DanBar1971/open-lab-monitor/pcb/eagle/ambient-humidity-temp-therimstor-REVBsch.png

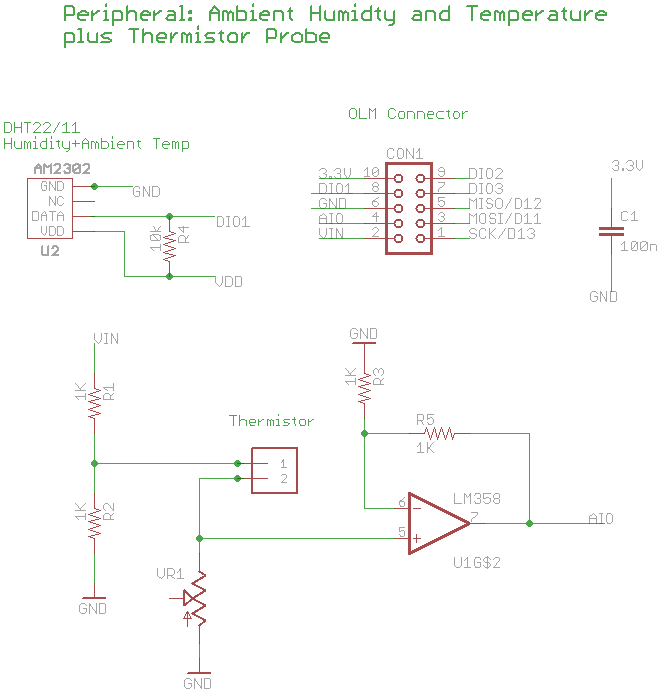
pcb/eagle/ambient-humidity-temp-therimstor-REVBsch.png
