DanBar1971/open-lab-monitor/pcb/eagle/OLM-base-v.REV-3-SMT-Board.png

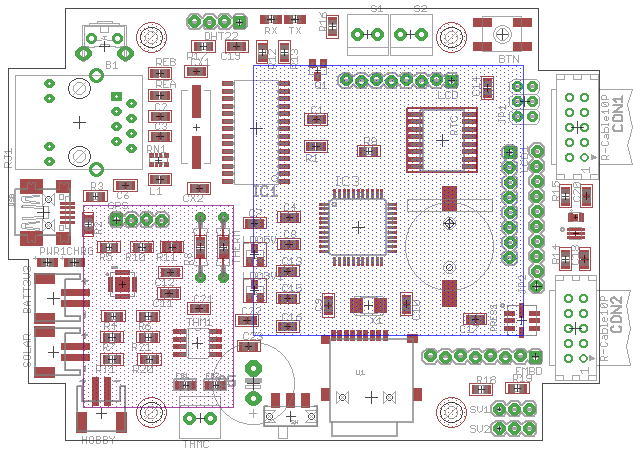
pcb/eagle/OLM-base-v.REV-3-SMT-Board.png
