DanBar1971/open-lab-monitor/pcb/eagle/OLM-base-v.REVH-SMT.png

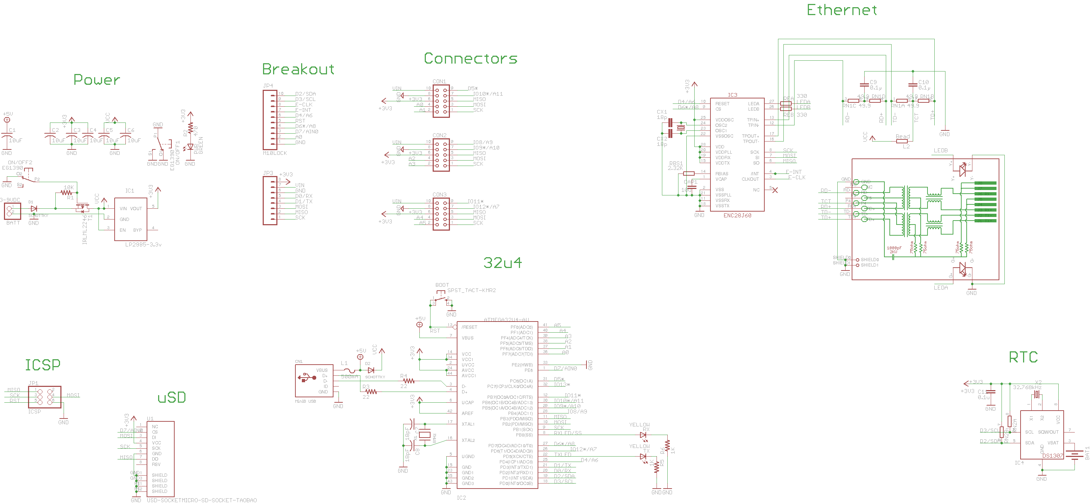
pcb/eagle/OLM-base-v.REVH-SMT.png
