DanBar1971/open-lab-monitor/pcb/eagle/OLM-base_v.REVG.png

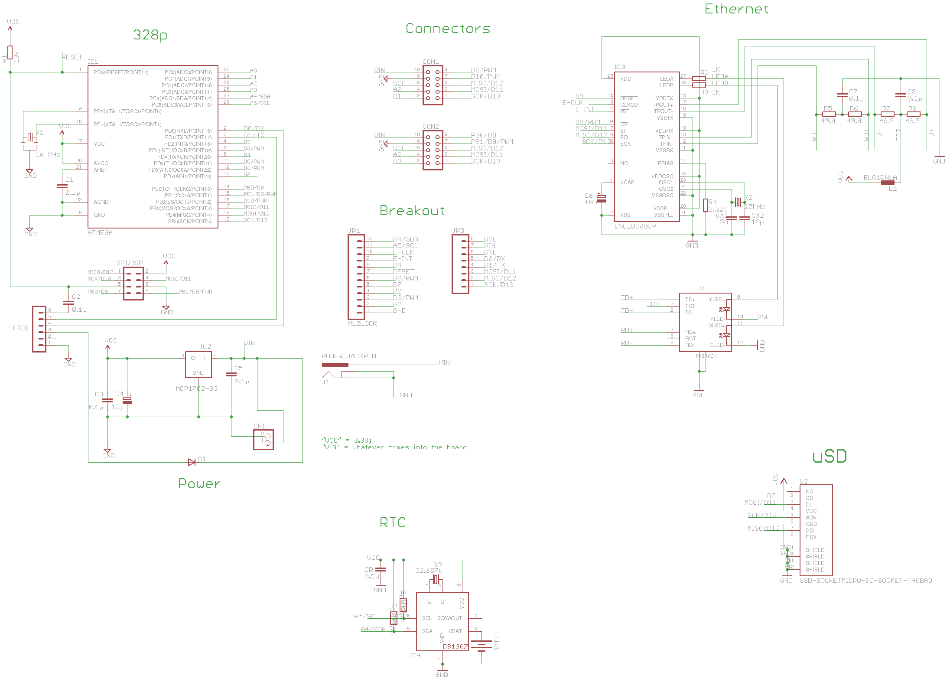
pcb/eagle/OLM-base_v.REVG.png
