DanBar1971/open-lab-monitor/pcb/eagle/olm-periph-probe+ambient+boostREVB.png

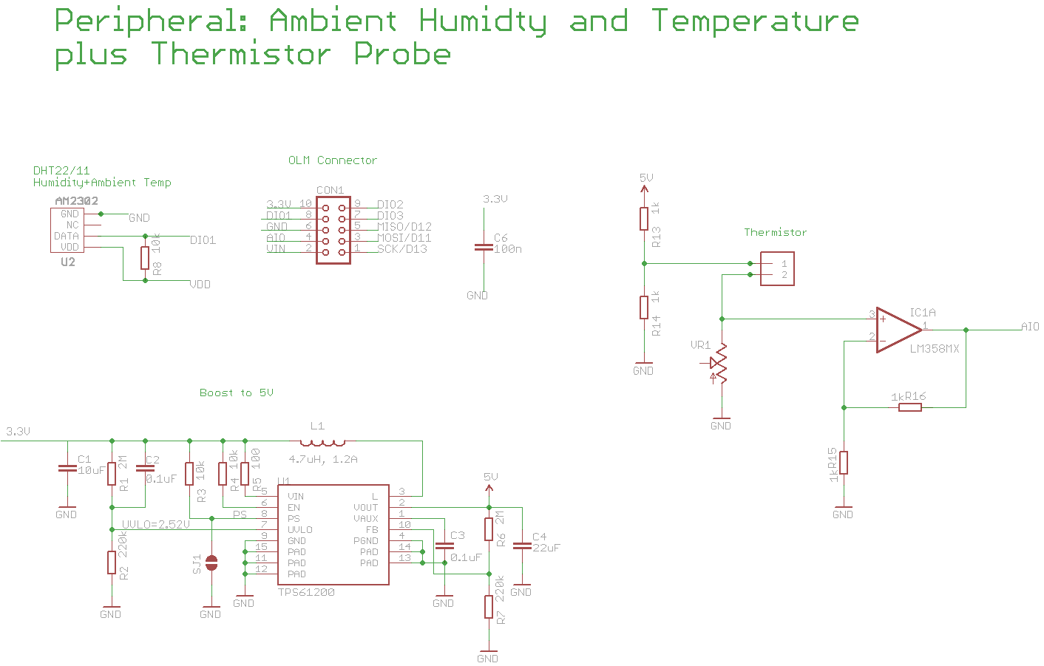
pcb/eagle/olm-periph-probe+ambient+boostREVB.png
