DanBar1971/open-lab-monitor/pcb/eagle/OLM-REV-5-brd.png

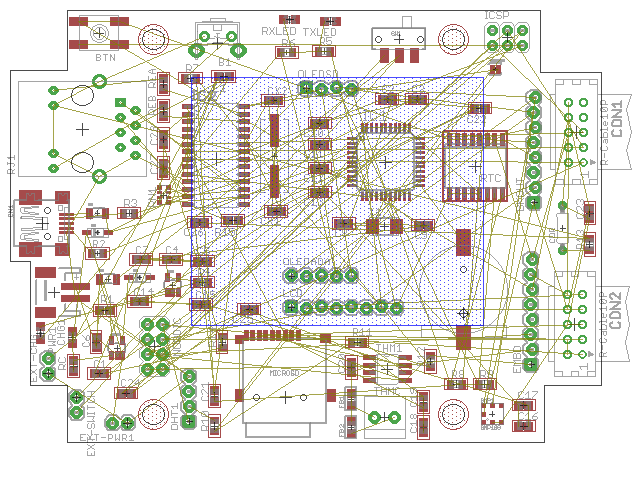
pcb/eagle/OLM-REV-5-brd.png
