DanBar1971/open-lab-monitor/pcb/eagle/OLM-REV-5-sch.png

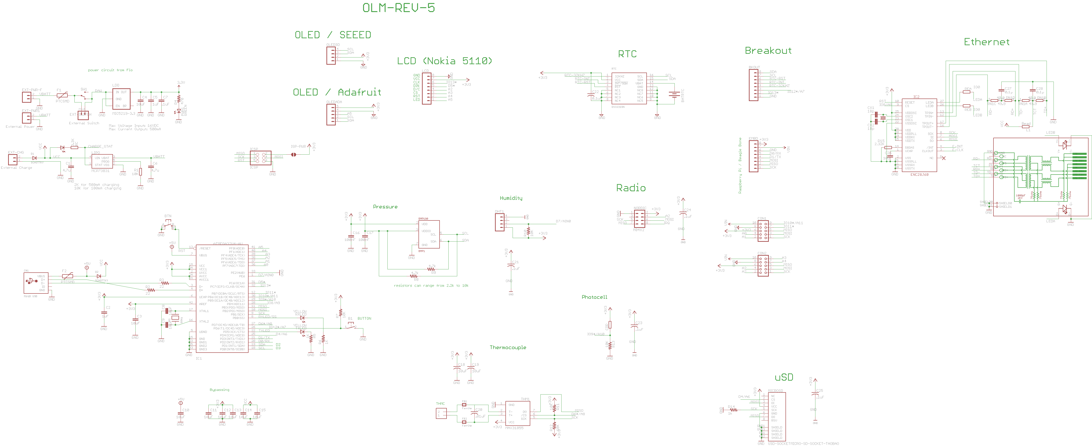
pcb/eagle/OLM-REV-5-sch.png
