DanBar1971/open-lab-monitor/pcb/eagle/OLMv11brd.png

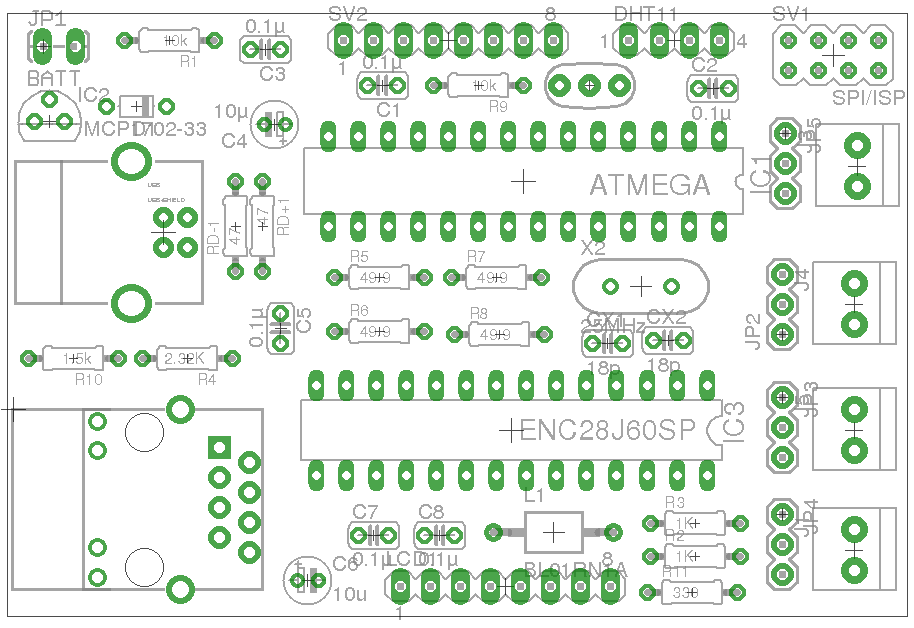
pcb/eagle/OLMv11brd.png
