DanBar1971/open-lab-monitor/pcb/eagle/OLMv11sch.png

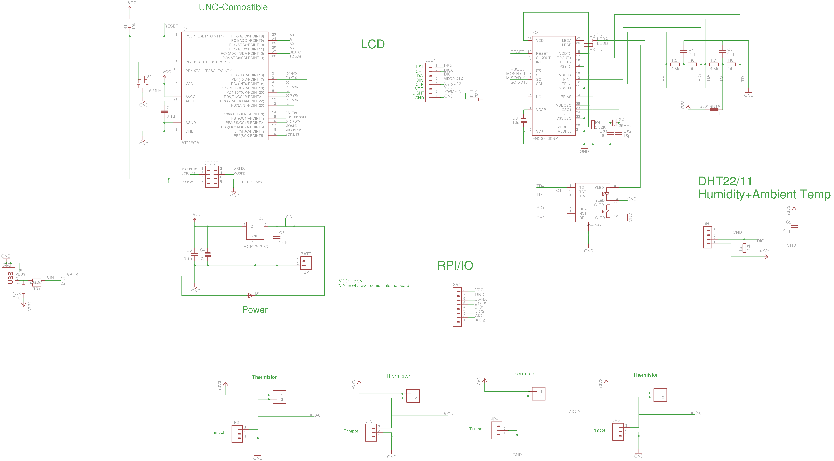
pcb/eagle/OLMv11sch.png
