DanBar1971/open-lab-monitor/pcb/eagle/OpenLux-v2-brd.png

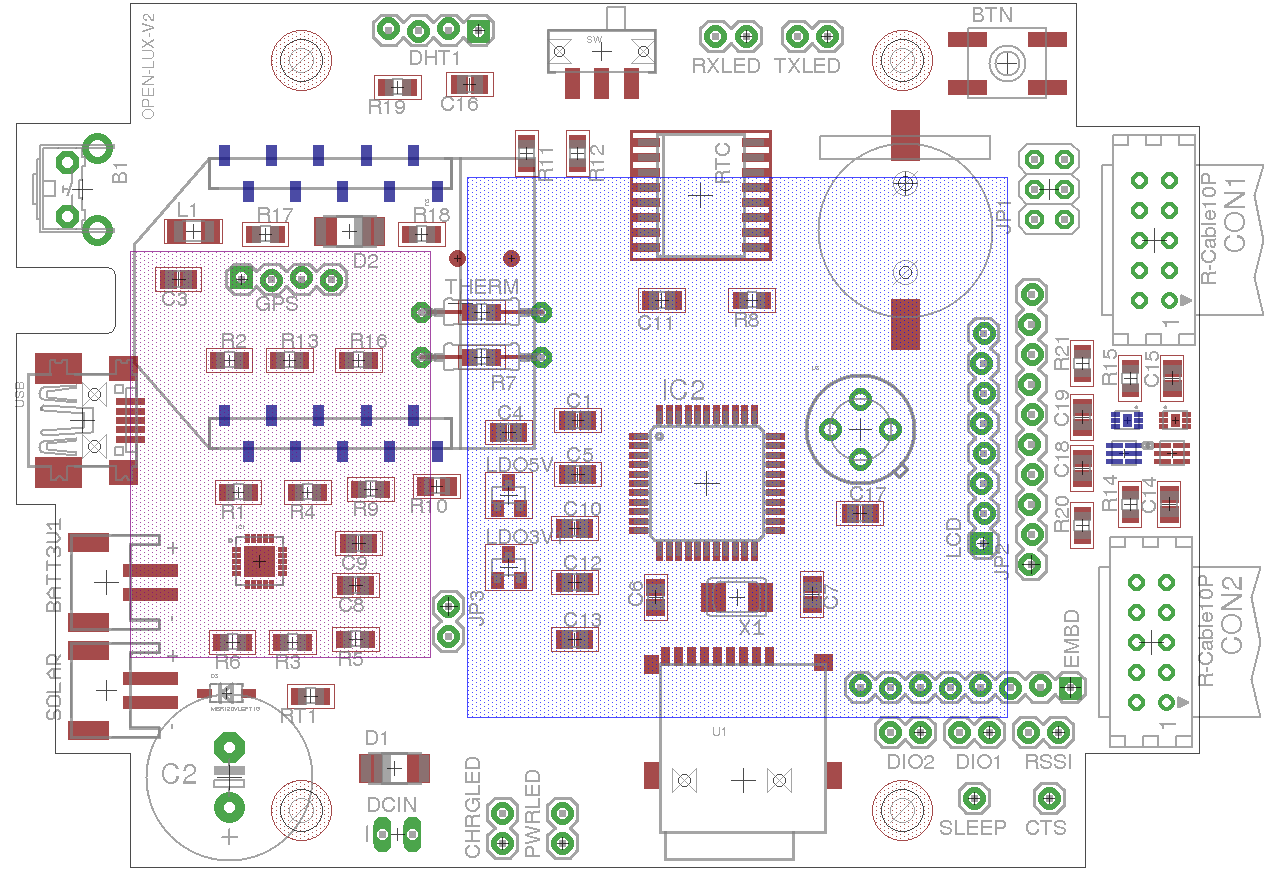
pcb/eagle/OpenLux-v2-brd.png
