DanBar1971/open-lab-monitor/pcb/eagle/OpenLux-v2-sch.png

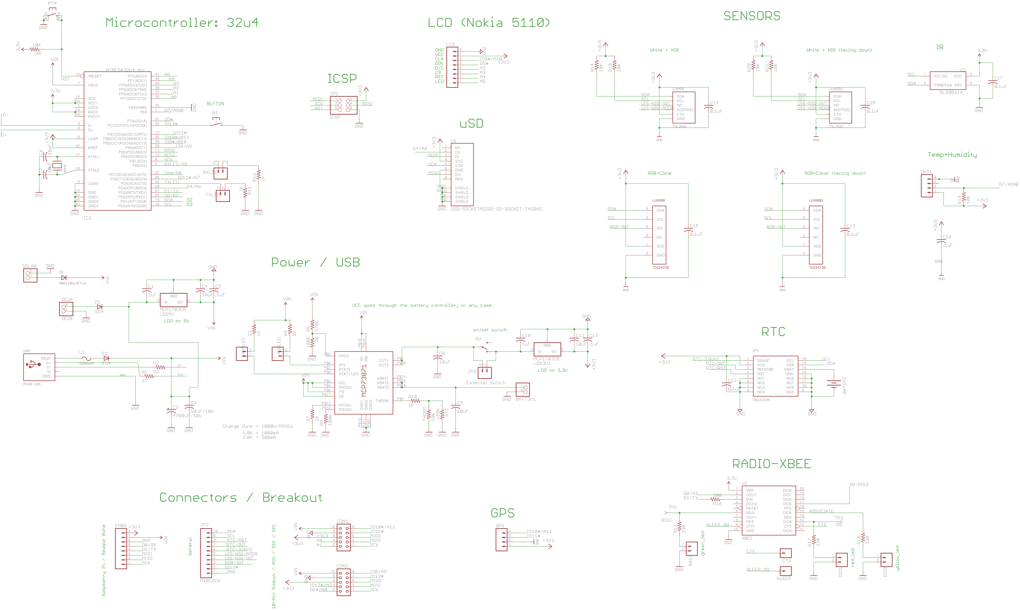
pcb/eagle/OpenLux-v2-sch.png
