DanBar1971/open-lab-monitor/pcb/eagle/VUSB/open-lab-VUSB-A-board.png

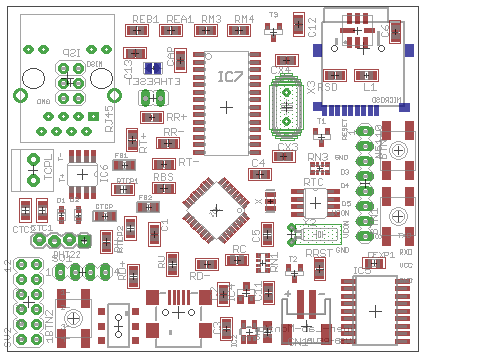
pcb/eagle/VUSB/open-lab-VUSB-A-board.png
