DanBar1971/open-lab-monitor/pcb/eagle/OpenLux-v1a.brd

## EAGLE design pcb/eagle/OpenLux-v1a.brd (2013-09-16)

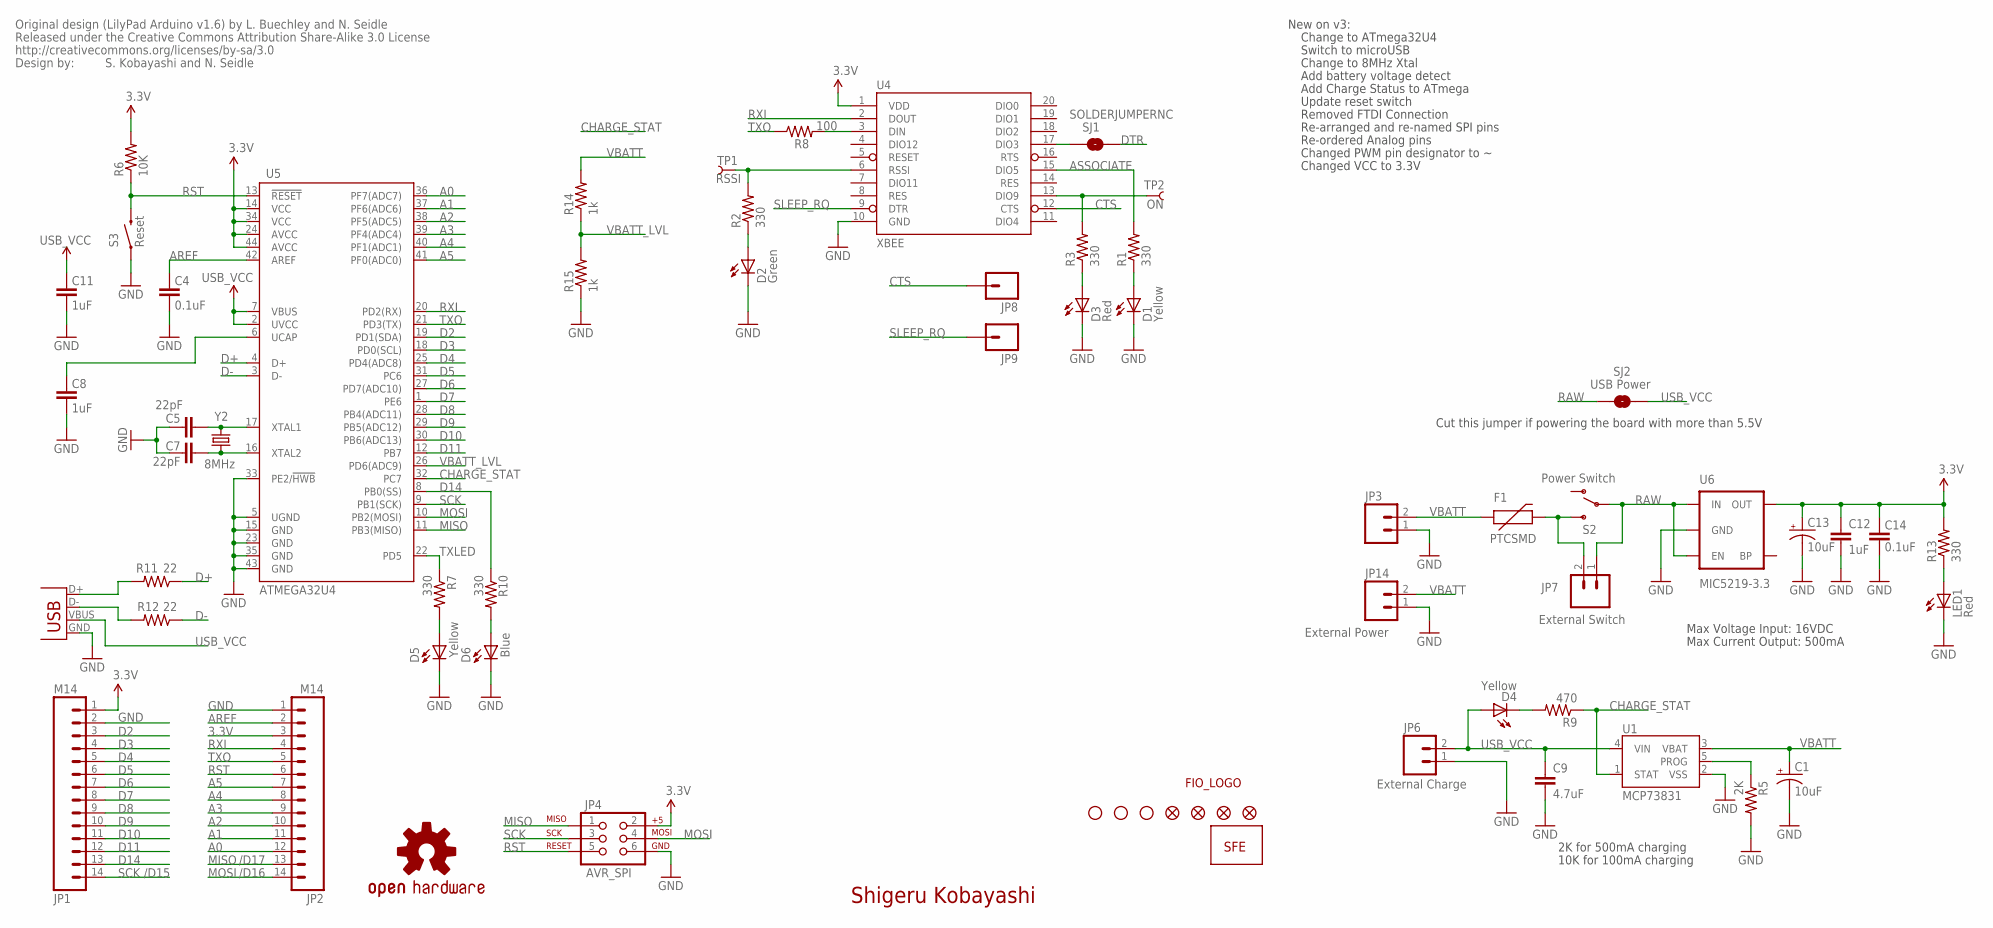
[picture p30: schematic OpenLux-v1a.sch]

Parts:
C1, C13: 10uF; EIA3216
C4, C14: 0.1uF; 0402-CAP
C5, C7: 22pF; 0402-CAP
C8, C11, C12: 1uF; 0402-CAP
C9: 4.7uF; 0402-CAP
D1, D4, D5: Yellow; LED-0603
D2: Green; LED-0603
D3: Red; LED-0603
D6: Blue; LED-0603
F1: PTCSMD; PTC-1206
JP1, JP2: M14; 1X14
JP3: M02-JST-2MM-SMT; JST-2-SMD
JP4: AVR_SPI; 2X3
JP5, JP16, JP17: STAND-OFF
JP6: External Charge; 1X02
JP7: External Switch; 1X02
JP8, JP9: M01PTH; 1X01
JP10, JP11, JP12, JP13: FIDUCIALUFIDUCIAL; FIDUCIAL-1X2
JP14: External Power; 1X02
LED1: Red; LED-0603
R1, R2, R3, R7, R10, R13: 330; 0402-RES
R5: 2K; 0402-RES
R6: 10K; 0402-RES
R8: 100; 0402-RES
R9: 470; 0402-RES
R11, R12: 22; 0402-RES
R14, R15: 1k; 0402-RES
S2: Power Switch; AYZ0202
S3: Reset; TACTILE_SWITCH_SMD
SJ1: SOLDERJUMPERNC; SJ_2S
SJ2: USB Power; SJ_2S-TRACE
TP1: RSSI; PAD.03X.05
TP2: ON; PAD.03X.05
U1: MCP73831; SOT23-5
U4: XBEE; XBEE-SMD
U5: ATMEGA32U4; QFN-44-NOPAD
U6: MIC5219-3.3; SOT23-5
U$1: LOGO-SFENEW; SFE-NEW-WEBLOGO
U$2: OSHW-LOGOS; OSHW-LOGO-S
U$3: CREATIVE_COMMONS
U$6: FIO_LOGOV2; FUNNEL_LOGO_BOTTOM_V2
X2: USB-MICROB
Y2: 8MHz; CRYSTAL-SMD-5X3

Connections:
3.3V: C12.1, C13.A (+), C14.2, JP1.1, JP2.3, JP4.2, R6.2, R13.2, U4.1 (VDD), U5.14 (VCC), U5.24 (AVCC), U5.34 (VCC), U5.44 (AVCC), U6.5 (OUT)
A0: JP2.12, U5.36 (PF7(ADC7))
A1: JP2.11, U5.37 (PF6(ADC6))
A2: JP2.10, U5.38 (PF5(ADC5))
A3: JP2.9, U5.39 (PF4(ADC4))
A4: JP2.8, U5.40 (PF1(ADC1))
A5: JP2.7, U5.41 (PF0(ADC0))
AREF: C4.2, JP2.2, U5.42 (AREF)
ASSOCIATE: R1.2, U4.15 (DIO5)
CHARGE_STAT: R9.1, U1.1 (STAT), U5.32 (PC7)
CTS: JP8.1, U4.12 (CTS)
D2: JP1.3, U5.19 (PD1(SDA))
D3: JP1.4, U5.18 (PD0(SCL))
D4: JP1.5, U5.25 (PD4(ADC8))
D5: JP1.6, U5.31 (PC6)
D6: JP1.7, U5.27 (PD7(ADC10))
D7: JP1.8, U5.1 (PE6)
D8: JP1.9, U5.28 (PB4(ADC11))
D9: JP1.10, U5.29 (PB5(ADC12))
D10: JP1.11, U5.30 (PB6(ADC13))
D11: JP1.12, U5.12 (PB7)
D14: JP1.13, R10.1, U5.8 (PB0(SS))
D+: R11.1, U5.4 (D+)
D-: R12.1, U5.3 (D-)
DTR: SJ1.2
GND: C1.C (-), C4.1, C5.2, C7.2, C8.1, C9.2, C11.1, C12.2, C13.C (-), C14.1, D1.C, D2.C, D3.C, D5.C, D6.C, JP1.2, JP2.1, JP3.1, JP4.6, JP6.1, JP14.1, LED1.C, R5.2, R15.1, S3.1, U1.2 (VSS), U4.10 (GND), U5.5 (UGND), U5.15 (GND), U5.23 (GND), U5.33 (PE2/!HWB), U5.35 (GND), U5.43 (GND), U6.2 (GND), X2.GND
MISO: JP2.13, JP4.1, U5.11 (PB3(MISO))
MOSI: JP2.14, JP4.4, U5.10 (PB2(MOSI))
unnamed: R3.2, TP2.P$1, U4.13 (DIO9)
unnamed: D1.A, R1.1
unnamed: D2.A, R2.1
unnamed: R2.2, TP1.P$1, U4.6 (RSSI)
unnamed: D3.A, R3.1
unnamed: R8.2, U4.3 (DIN)
unnamed: D4.C, R9.2
unnamed: F1.2, JP7.2, S2.3 (S)
unnamed: R5.1, U1.5 (PROG)
unnamed: SJ1.1, U4.17 (DIO3)
unnamed: D5.A, R7.2
unnamed: C7.1, U5.16 (XTAL2), Y2.1
unnamed: C5.1, U5.17 (XTAL1), Y2.3 (2)
unnamed: D6.A, R10.2
unnamed: R12.2, X2.D-
unnamed: R11.2, X2.D+
unnamed: LED1.A, R13.1
RAW: JP7.1, S2.2, SJ2.1, U6.1 (IN), U6.3 (EN)
RST: JP2.6, JP4.5, R6.1, S3.3 (2), U5.13 (!RESET)
RXI: JP2.4, U4.2 (DOUT), U5.20 (PD2(RX))
SCK: JP1.14, JP4.3, U5.9 (PB1(SCK))
SLEEP_RQ: JP9.1, U4.9 (DTR)
TXLED: R7.1, U5.22 (PD5)
TXO: JP2.5, R8.1, U5.21 (PD3(TX))
UCAP: C8.2, U5.6 (UCAP)
USB_VCC: C9.1, C11.2, D4.A, JP6.2, SJ2.2, U1.4 (VIN), U5.2 (UVCC), U5.7 (VBUS), X2.VBUS
VBATT: C1.A (+), F1.1, JP3.2, JP14.2, R14.2, U1.3 (VBAT)
VBATT_LVL: R14.1, R15.2, U5.26 (PD6(ADC9))

Notes on the sheet:
Shigeru Kobayashi
/D16
/D17
/D15
Original design (LilyPad Arduino v1.6) by L. Buechley and N. Seidle
S. Kobayashi and N. Seidle
Change to ATmega32U4
Switch to microUSB
New on v3:
Change to 8MHz Xtal
Max Voltage Input: 16VDC
Max Current Output: 500mA
Cut this jumper if powering the board with more than 5.5V
2K for 500mA charging
10K for 100mA charging
Add battery voltage detect
Add Charge Status to ATmega
Update reset switch
Removed FTDI Connection
Re-arranged and re-named SPI pins
Re-ordered Analog pins
Changed PWM pin designator to ~
Changed VCC to 3.3V
