DanBar1971/open-lab-monitor/pcb/eagle/OpenLux-v1a.brd

## EAGLE design pcb/eagle/OpenLux-v1a.brd (continued)

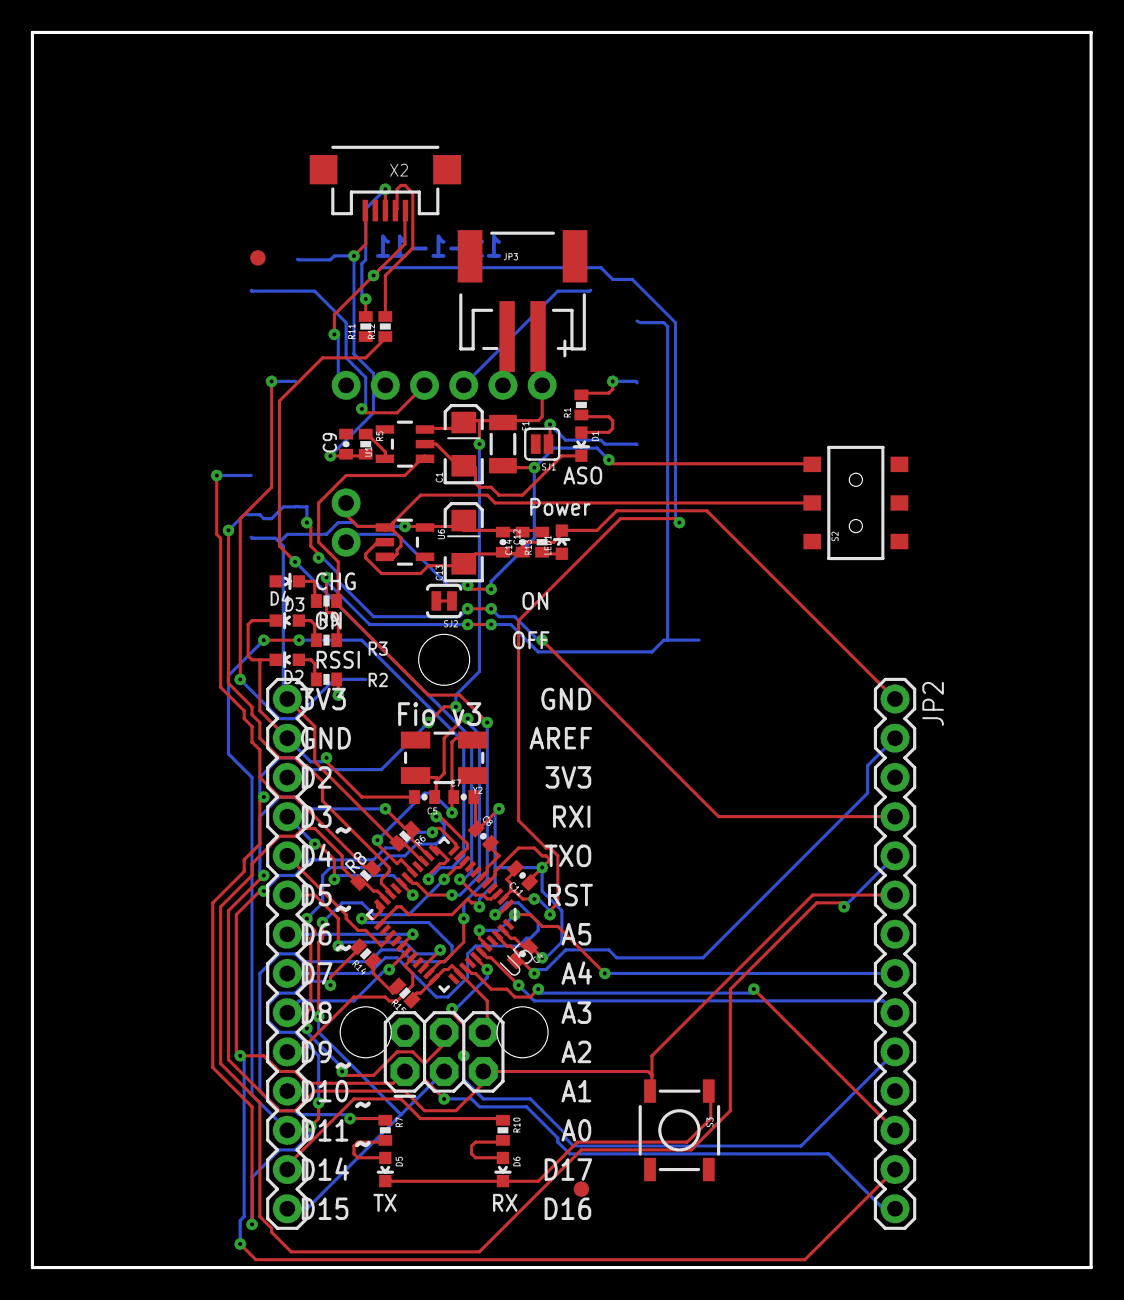
[picture p31: board OpenLux-v1a.brd from above]

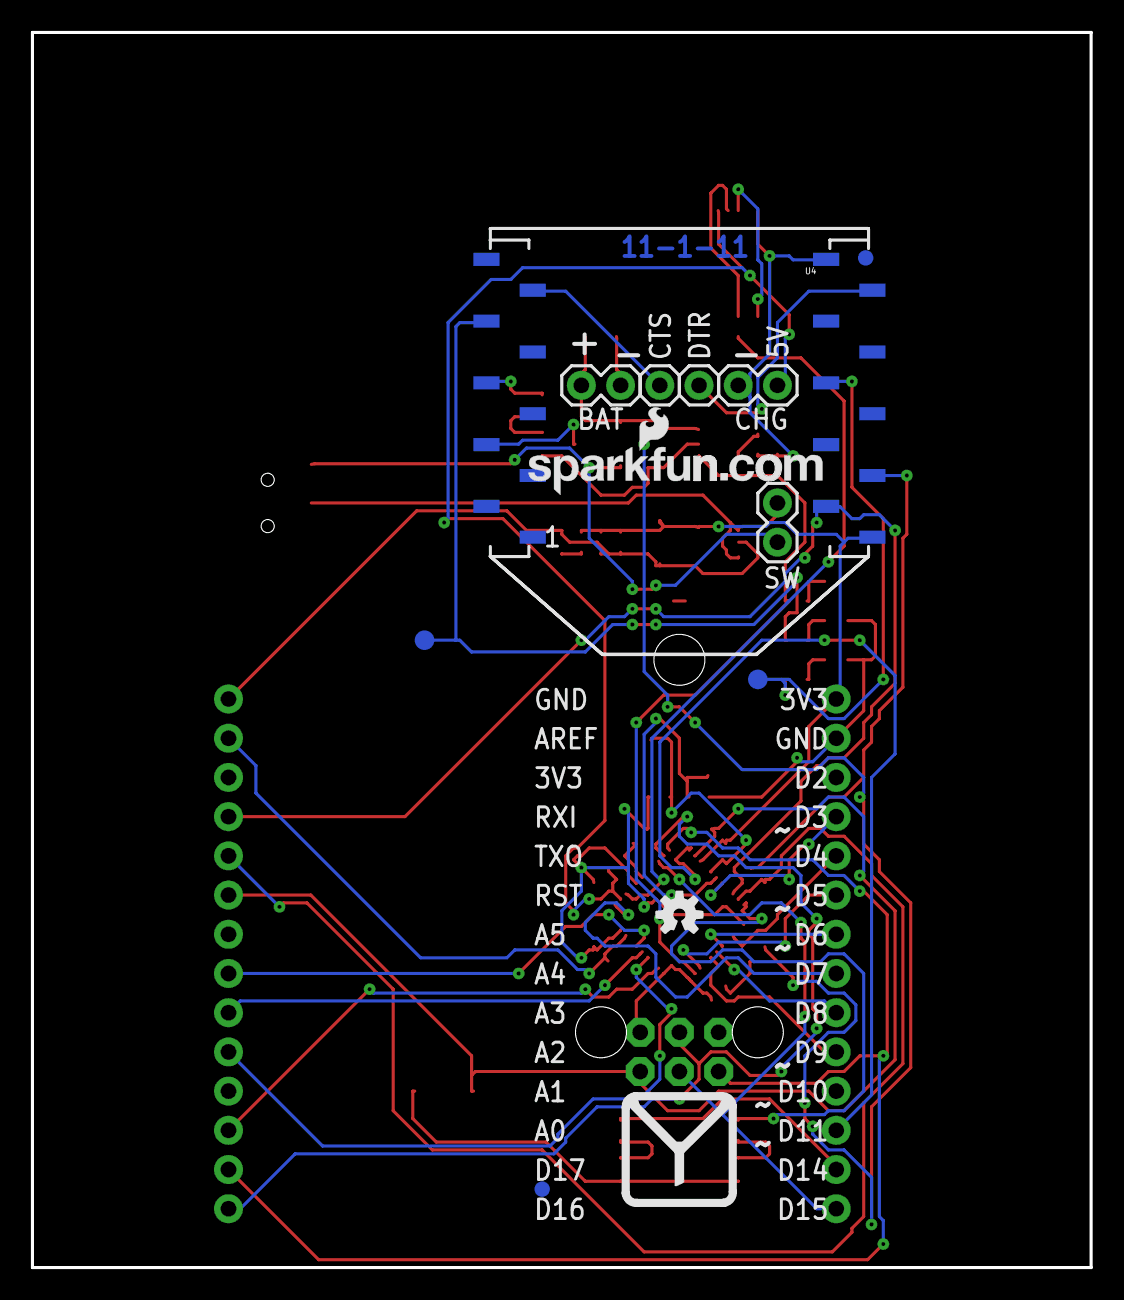
[picture p32: board OpenLux-v1a.brd from below]

Board: 2 copper layers, 68.6 x 80.0 mm, 64 parts (12 on the bottom side), 55 nets.
