DanBar1971/open-lab-monitor/pcb/eagle/thermal-flashlight.brd

## EAGLE design pcb/eagle/thermal-flashlight.brd (2013-09-16)

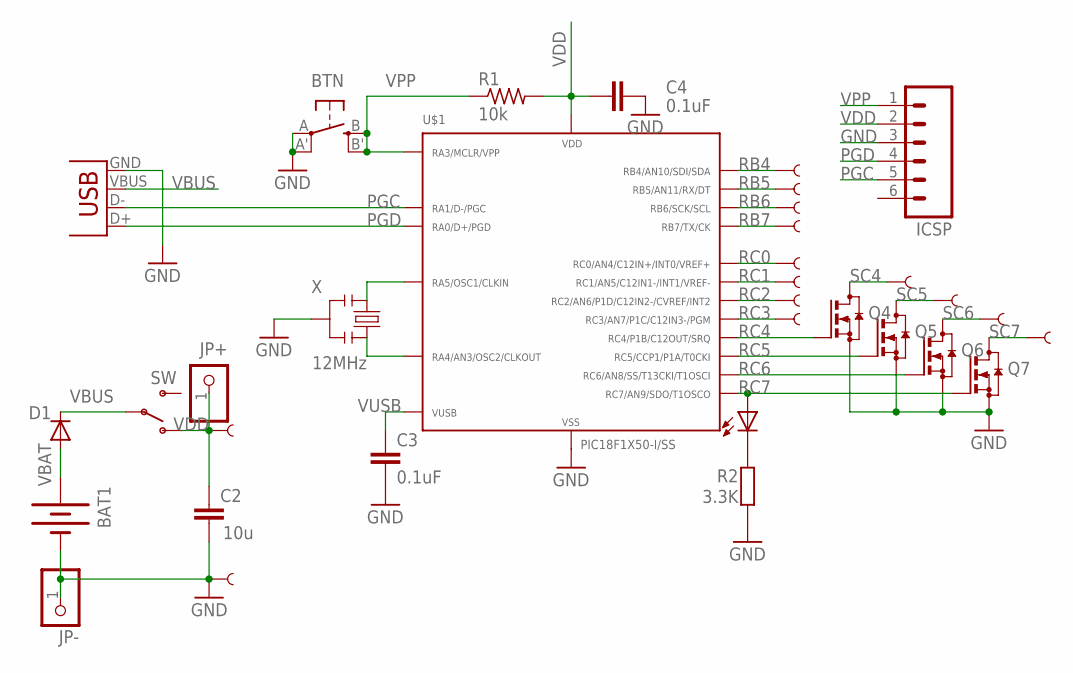
[picture p33: schematic thermal-flashlight.sch]

Parts:
BAT1: BATTERY20MM_4LEGS; BATTCON_20MM_4LEGS
BTN: EVQQ2; EVQ-Q2
C2: 10u; C0805
C3, C4: 0.1uF; C0805
D1: DIODESOT23; SOT23-3
ICSP: M06SIP; 1X06
JP+: PINHD-1X1CB; 1X01-CLEANBIG
JP-: PINHD-1X1CB; 1X01-CLEANBIG
LED: 0805; CHIPLED_0805
PB4: SEWTAP61; PETAL-SMALL-2SIDE1
PB5, PB6, PB7: SEWTAP6; PETAL-SMALL-2SIDE1
PC0, PC1, PC2, PC3: SEWTAP6; PETAL-SMALL-2SIDE1
PG: SEWTAP6; PETAL-SMALL-2SIDE11
PSC4, PSC5, PSC6, PSC7: SEWTAP6; PETAL-SMALL-2SIDE1
PVCC: SEWTAP6; PETAL-SMALL-2SIDE11
Q4, Q5, Q6, Q7: BSS123; SOT23
R1: 10k; R0805@1
R2: 3.3K; R0805
SW: SPDT; SWITCH-SPDT-SMD
U$1: PIC18F1X50-I/SS; SSOP20
X: 12MHz; RESONATOR-SMD
X1: USBSMD; USB-MINIB

Connections:
GND: BAT1.2 (-), BTN.A, BTN.A' (P1), C2.2, C3.2, C4.2, ICSP.3, JP-.1, PG.1, Q4.2 (S), Q5.2 (S), Q6.2 (S), Q7.2 (S), R2.1, U$1.20, X.2, X1.GND
unnamed: U$1.2, X.1
unnamed: U$1.3, X.3
unnamed: LED.C, R2.2
PGC: ICSP.5, U$1.18, X1.D-
PGD: ICSP.4, U$1.19, X1.D+
RB4: PB4.1, U$1.13
RB5: PB5.1, U$1.12
RB6: PB6.1, U$1.11
RB7: PB7.1, U$1.10
RC0: PC0.1, U$1.16
RC1: PC1.1, U$1.15
RC2: PC2.1, U$1.14
RC3: PC3.1, U$1.7
RC4: Q4.1 (G), U$1.6
RC5: Q5.1 (G), U$1.5
RC6: Q6.1 (G), U$1.8
RC7: LED.A, Q7.1 (G), U$1.9
SC4: PSC4.1, Q4.3 (D)
SC5: PSC5.1, Q5.3 (D)
SC6: PSC6.1, Q6.3 (D)
SC7: PSC7.1, Q7.3 (D)
VBAT: BAT1.1 (+), D1.1 (A)
VBUS: D1.3 (C), SW.2, X1.VBUS
VDD: C2.1, C4.1, ICSP.2, JP+.1, PVCC.1, R1.2, SW.1 (O), U$1.1
VPP: BTN.B (S), BTN.B' (S1), ICSP.1, R1.1, U$1.4
VUSB: C3.1, U$1.17

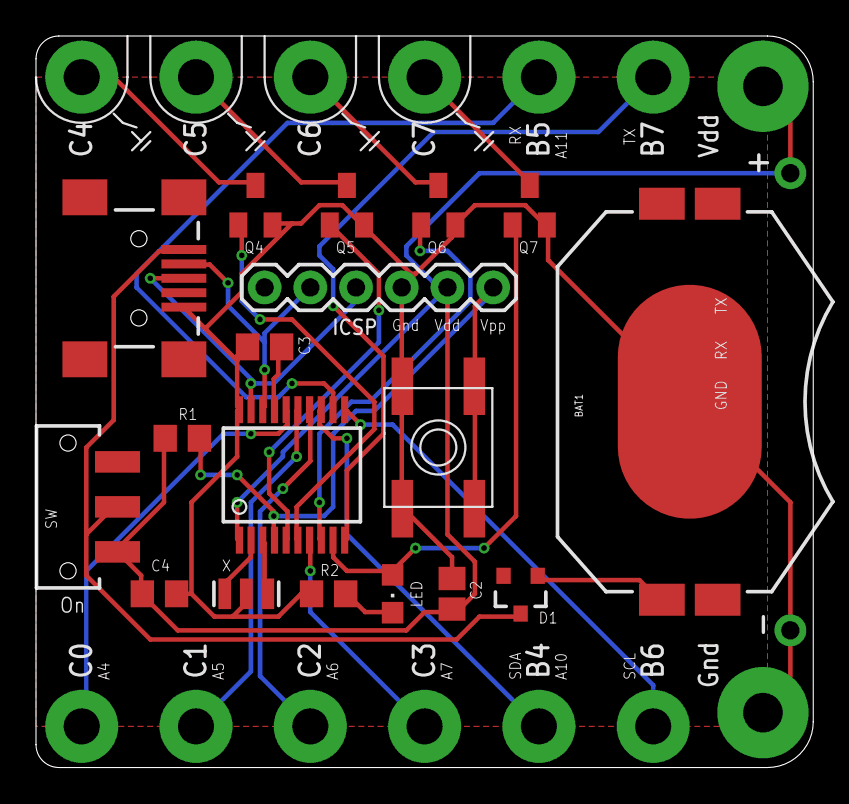
[picture p34: board thermal-flashlight.brd from above]

Board: 2 copper layers, 43.2 x 40.6 mm, 34 parts (0 on the bottom side), 27 nets.
