DanBar1971/open-lab-monitor/pcb/eagle/OLM-base-v.REV-I-SMT.brd

## EAGLE design pcb/eagle/OLM-base-v.REV-I-SMT.brd (2013-07-30)

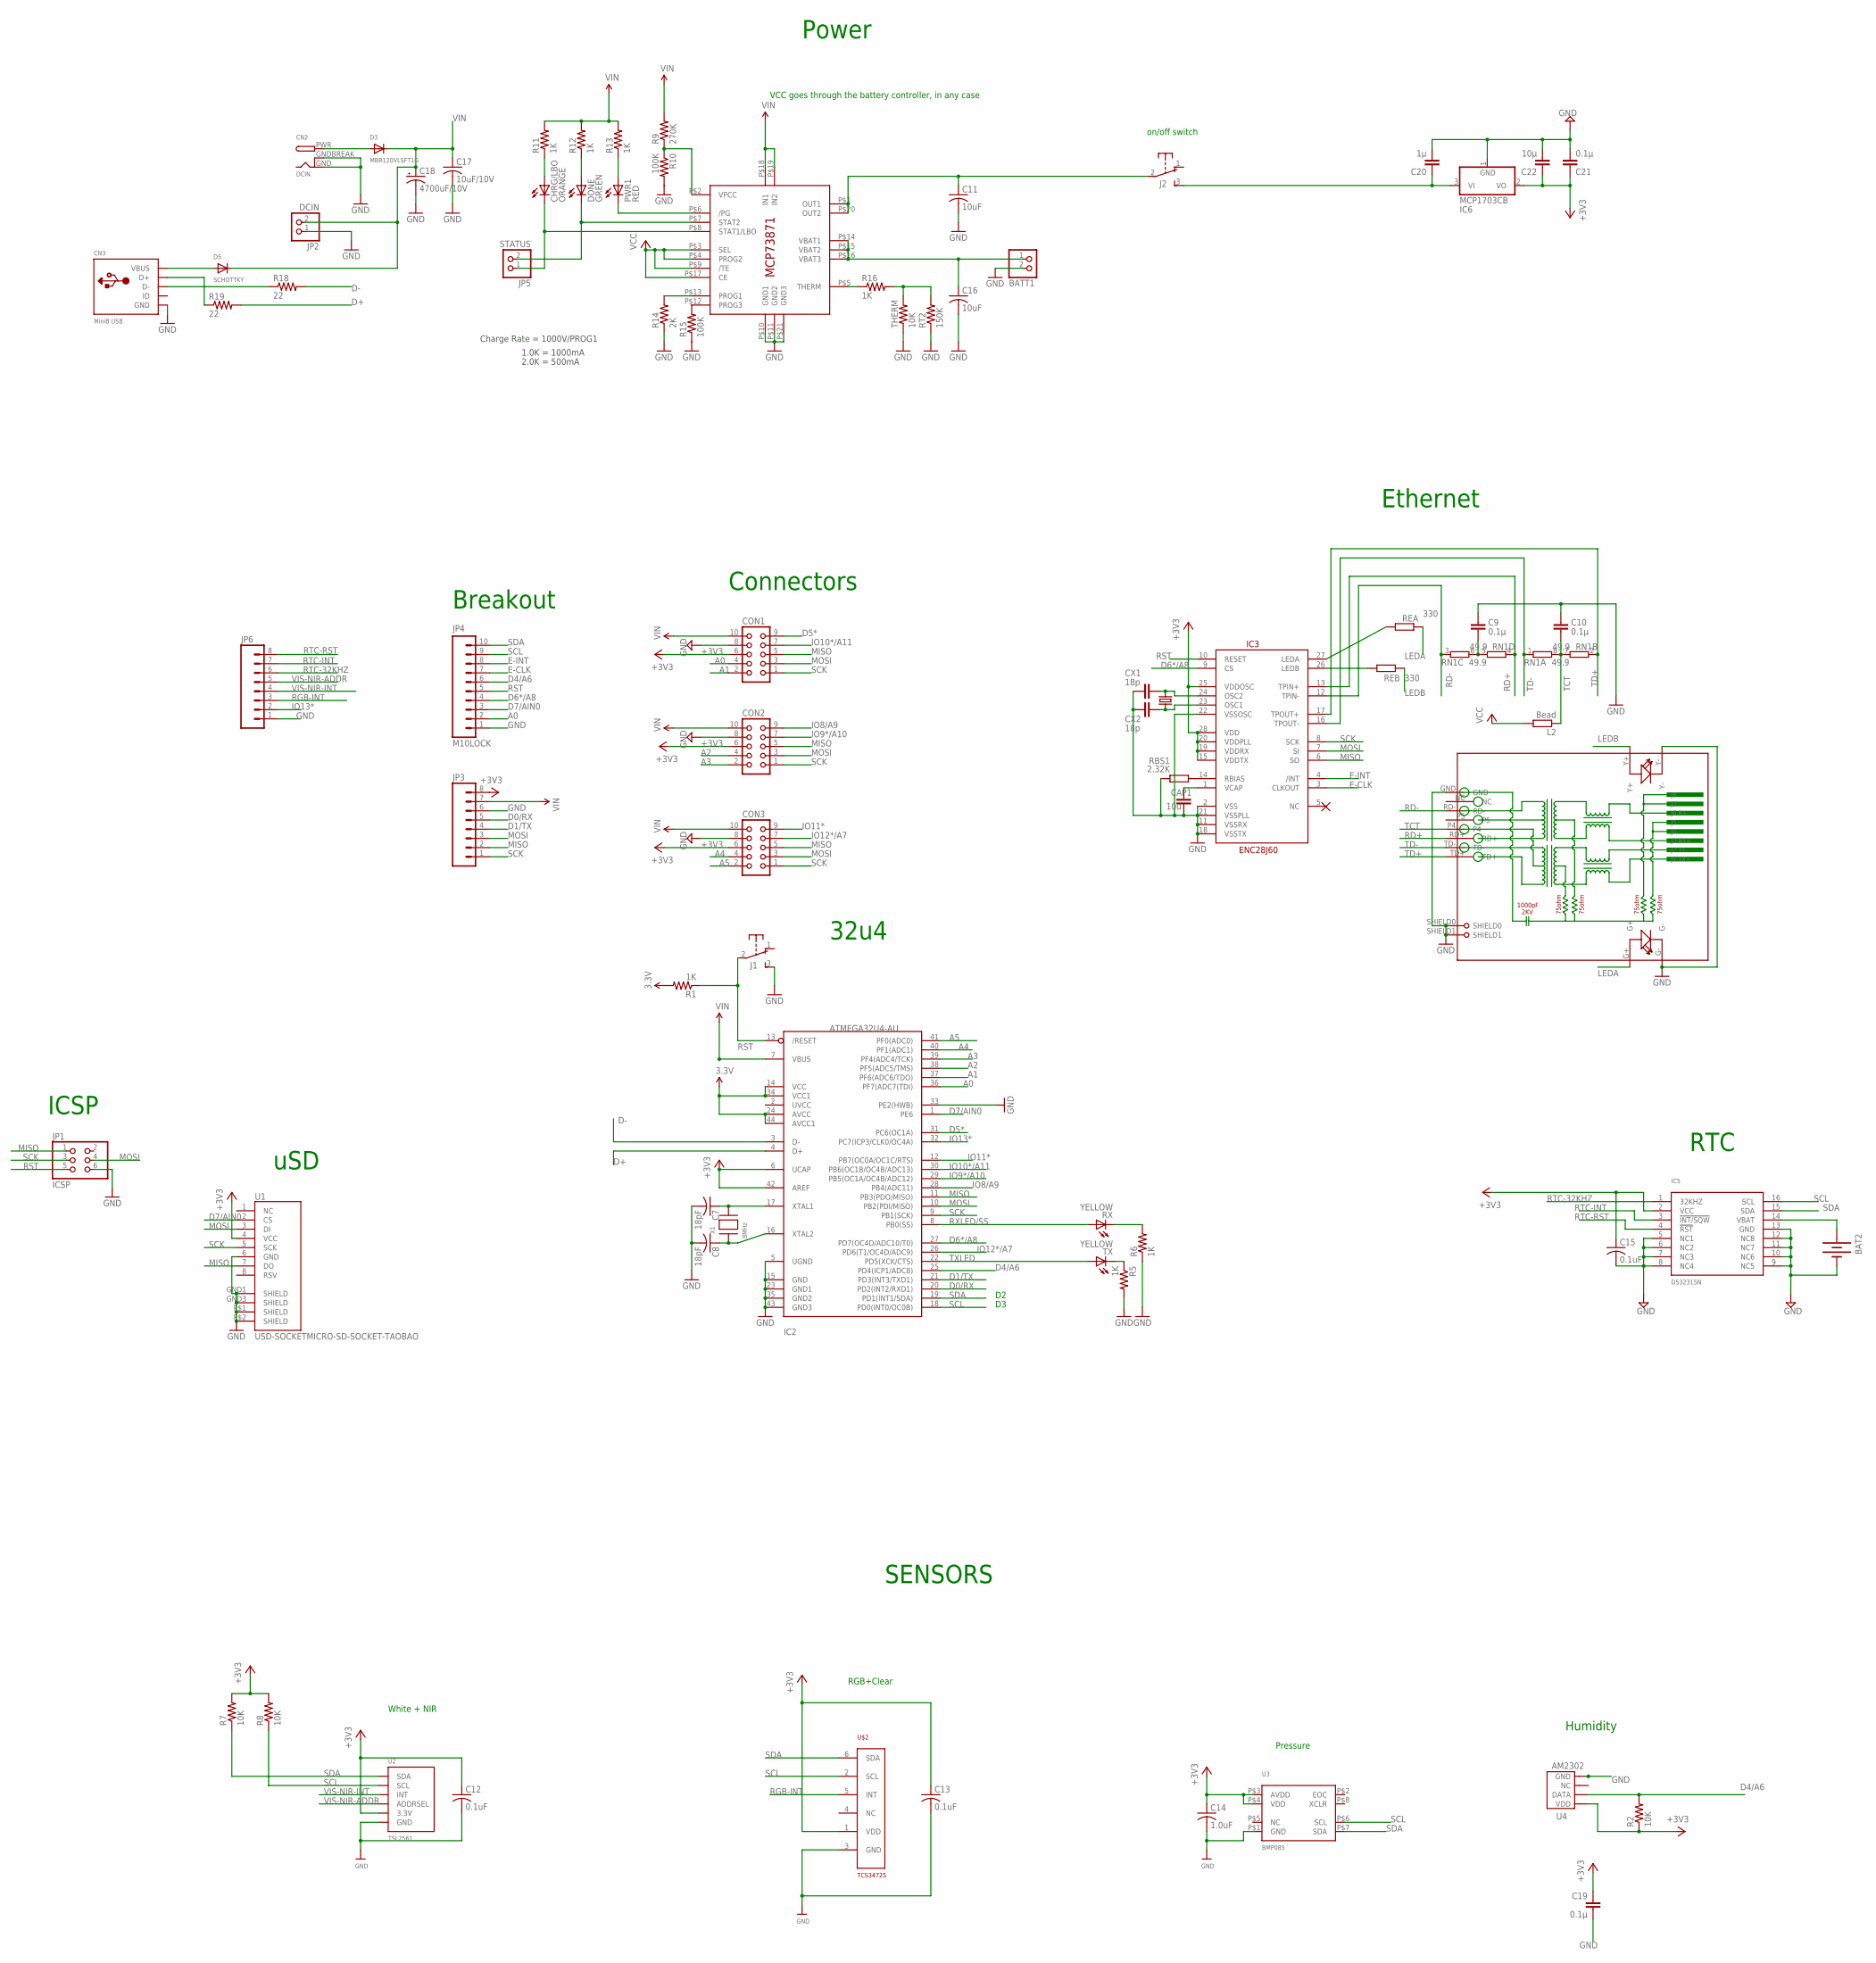
[picture p35: schematic OLM-base-v.REV-I-SMT.sch]

Parts:
BAT2: BATTERYBATTERY_12MM_SMT; BATTCON_12MM_SMT
BATT1: JST_2PIN-SMT-RA; JST-PH-2-SMT-RA
C7, C8: 18pF; C0805K
C9, C10: 0.1µ; C0805
C11, C16: 10uF; C0805K
C12, C13, C15: 0.1uF; C0805
C14: 1.0uF; C0805
C17: 10uF/10V; C0805K
C18: 4700uF/10V; E5-13
C19: 0.1µ; C025-024X044
C20: 1µ; C0603
C21: 0.1µ; C0603
C22: 10µ; 0603-CAP
CAP1: 10u; C0805
CHRG/LBO: ORANGE; CHIP-LED0805
CN2: DCIN; DCJACK_1.3MM_PTH
CN3: MiniB USB; USB-MINIB_LARGER
CON1, CON2, CON3: CON10L
CX1, CX2: 18p; C0805
D3: MBR120VLSFT1G; SOD-123
D5: SCHOTTKY; SOD-123
DONE: GREEN; CHIP-LED0805
IC2: ATMEGA32U4-AU; TQFP44
IC3: ENC28J60; SOIC28WLONG
IC4: MCP73871; QFN20_4MM
IC5: DS3231SN; SO16W
IC6: MCP1703CB; SOT23
J1, J2: EG1206
JP1: ICSP; 2X03
JP2: DCIN; 1X02_OVAL
JP3, JP6: M08LOCK; 1X08_LOCK
JP4: M10LOCK; 1X10_LOCK
JP5: STATUS; 1X02_OVAL
L2: Bead; R0805
PWR1: RED; CHIP-LED0805
R1, R5, R6, R11, R12, R13: 1K; R0805
R2, R7, R8: 10K; R0805
R9: 270K; R0805
R10, R15: 100K; R0805
R14: 2K; 0805-THM
R16: 1K; M0805
R18, R19: 22; R0805
RBS1: 2.32K; R0805
REA: 330; R0805
REB: 330; R0805
RJ1: HR911105A
RN1: 49.9; EXB38V
RT2: 150K; M0805
RX: YELLOW; CHIPLED_0805
THERM: 10K; 0805-THM
TX: YELLOW; CHIPLED_0805
U1: USD-SOCKETMICRO-SD-SOCKET-TAOBAO; MICRO-SD-SOCKET-TAOBAO
U2: TSL2561; TSL2561_FN
U3: BMP085
U4: AM2302
U$2: TCS34725; DFN-6
X1: 8MHz; NX5032
X2A: 25MHz; CRYSTAL-SMD-10.5X4.8-2PIN

Connections:
+3V3: C12.1, C13.1, C14.1, C15.1, C19.1, C21.1, C22.1, CON1.6, CON2.6, CON3.6, IC2.6 (UCAP), IC2.42 (AREF), IC3.15 (VDDTX), IC3.19 (VDDRX), IC3.20 (VDDPLL), IC3.25 (VDDOSC), IC3.28 (VDD), IC5.2 (VCC), IC6.2 (VO), JP3.8, R2.1, R7.2, R8.2, U1.4 (VCC), U2.VDD (3.3V), U3.P$3 (AVDD), U3.P$4 (VDD), U4.P$1 (VDD), U$2.1 (VDD)
A0: CON1.4, IC2.36 (PF7(ADC7(TDI)), JP4.2
A1: CON1.2, IC2.37 (PF6(ADC6/TDO))
A2: CON2.4, IC2.38 (PF5(ADC5/TMS))
A3: CON2.2, IC2.39 (PF4(ADC4/TCK))
A4: CON3.4, IC2.40 (PF1(ADC1))
A5: CON3.2, IC2.41 (PF0(ADC0))
BATT: BATT1.1 (2), C16.1, IC4.P$14 (VBAT1), IC4.P$15 (VBAT2), IC4.P$16 (VBAT3)
D0/RX: IC2.20 (PD2(INT2/RXD1)), JP3.5
D1/TX: IC2.21 (PD3(INT3/TXD1)), JP3.4
D4/A6: IC2.25 (PD4(ICP1/ADC8)), JP4.6, R2.2, U4.P$2 (DATA)
D5*: CON1.9, IC2.31 (PC6(OC1A))
D6*/A8: IC2.27 (PD7(OC4D/ADC10/T0)), IC3.9 (CS), JP4.4
D7/AIN0: IC2.1 (PE6), JP4.3, U1.2 (CS)
D+: IC2.4 (D+), R19.2
D-: IC2.3 (D-), R18.2
E-CLK: IC3.3 (CLKOUT), JP4.7
E-INT: IC3.4 (/INT), JP4.8
GND: BAT2.P$1 (-), BATT1.2 (1), C7.2, C8.2, C9.1, C10.1, C11.2, C12.2, C13.2, C14.2, C15.2, C16.2, C17.2, C18.-, C19.2, C20.2, C21.2, C22.2, CAP1.2, CN2.GND, CN2.GNDBREAK, CN3.GND, CON1.8, CON2.8, CON3.8, CX1.2, CX2.2, IC2.5 (UGND), IC2.15 (GND), IC2.23 (GND1), IC2.33 (PE2(HWB)), IC2.35 (GND2), IC2.43 (GND3), IC3.2 (VSS), IC3.11 (VSSRX), IC3.18 (VSSTX), IC3.21 (VSSPLL), IC3.22 (VSSOSC), IC4.P$10 (GND1), IC4.P$11 (GND2), IC4.P$21 (GND3), IC5.5 (NC1), IC5.6 (NC2), IC5.7 (NC3), IC5.8 (NC4), IC5.9 (NC5), IC5.10 (NC6), IC5.11 (NC7), IC5.12 (NC8), IC5.13 (GND), IC6.1 (GND), J1.3 (S), JP1.6, JP2.1, JP3.6, JP4.1, JP6.1, R5.2, R6.1, R10.2, R14.1, R15.1, RBS1.1, RJ1.G-, RJ1.GND, RJ1.SHIELD0, RJ1.SHIELD1, RJ1.Y-, RT2.1, THERM.1, U1.6 (GND), U1.GND1 (SHIELD), U1.GND3 (SHIELD), U1.P$1 (SHIELD), U1.P$2 (SHIELD), U2.VSS (GND), U3.P$1 (GND), U4.P$4 (GND), U$2.3 (GND)
IO8/A9: CON2.9, IC2.28 (PB4(ADC11))
IO9*/A10: CON2.7, IC2.29 (PB5(OC1A/OC4B/ADC12))
IO10*/A11: CON1.7, IC2.30 (PB6(OC1B/OC4B/ADC13))
IO11*: CON3.9, IC2.12 (PB7(OC0A/OC1C/RTS))
IO12*/A7: CON3.7, IC2.26 (PD6(T1/OC4D/ADC9))
IO13*: IC2.32 (PC7(ICP3/CLK0/OC4A)), JP6.2
LEDA: REA.2, RJ1.G+
LEDB: REB.2, RJ1.Y+
MISO: CON1.5, CON2.5, CON3.5, IC2.11 (PB3(PDO/MISO)), IC3.6 (SO), JP1.1, JP3.2, U1.7 (DO)
MOSI: CON1.3, CON2.3, CON3.3, IC2.10 (PB2(PDI/MISO)), IC3.7 (SI), JP1.4, JP3.3, U1.3 (DI)
unnamed: BAT2.P$2 (+), IC5.14 (VBAT)
unnamed: C7.1, IC2.17 (XTAL1), X1.P$2
unnamed: C8.1, IC2.16 (XTAL2), X1.P$1
unnamed: C9.2, RN1.5 (2), RN1.6 (2)
unnamed: R5.1, TX.C
unnamed: R6.2, RX.C
unnamed: IC3.27 (LEDA), REA.1
unnamed: IC3.26 (LEDB), REB.1
unnamed: CAP1.1, IC3.1 (VCAP)
unnamed: IC3.14 (RBIAS), RBS1.2
unnamed: CX1.1, IC3.24 (OSC2), X2A.P$2 (2)
unnamed: CX2.1, IC3.23 (OSC1), X2A.P$1 (1)
unnamed: IC4.P$2 (VPCC), R9.1, R10.1
unnamed: IC4.P$6 (/PG), PWR1.C
unnamed: DONE.C, IC4.P$7 (STAT2), JP5.2
unnamed: CHRG/LBO.C, IC4.P$8 (STAT1/LBO), JP5.1
unnamed: CHRG/LBO.A, R11.1
unnamed: DONE.A, R12.1
unnamed: PWR1.A, R13.1
unnamed: IC4.P$12 (PROG3), R15.2
unnamed: IC4.P$13 (PROG1), R14.2
unnamed: C11.1, IC4.P$1 (OUT1), IC4.P$20 (OUT2), J2.2
unnamed: IC4.P$5 (THERM), R16.1
unnamed: R16.2, RT2.2, THERM.2
unnamed: CN2.PWR, D3.A
unnamed: CN3.VBUS, D5.A
unnamed: CN3.D+, R19.1
unnamed: CN3.D-, R18.1
unnamed: C20.1, IC6.3 (VI), J2.3 (S)
RD+: IC3.13 (TPIN+), RJ1.RD+, RN1.4 (1)
RD-: IC3.12 (TPIN-), RJ1.RD-, RN1.3 (1)
RGB-INT: JP6.3, U$2.5 (INT)
RST: IC2.13 (/RESET), J1.2, JP1.5, JP4.5, R1.1
RTC-32KHZ: IC5.1 (32KHZ), JP6.6
RTC-INT: IC5.3 (!INT/SQW), JP6.7
RTC-RST: IC5.4 (!RST), JP6.8
RXLED/SS: IC2.8 (PB0(SS)), RX.A
SCK: CON1.1, CON2.1, CON3.1, IC2.9 (PB1(SCK)), IC3.8 (SCK), JP1.3, JP3.1, U1.5 (SCK)
SCL: IC2.18 (PD0(INT0/OC0B)), IC5.16 (SCL), JP4.9, R8.1, U2.CLK (SCL), U3.P$6 (SCL), U$2.2 (SCL)
SDA: IC2.19 (PD1(INT1/SDA)), IC5.15 (SDA), JP4.10, R7.1, U2.DATA (SDA), U3.P$7 (SDA), U$2.6 (SDA)
TCT: C10.2, L2.1, RJ1.P4, RN1.7 (2), RN1.8 (2)
TD+: IC3.17 (TPOUT+), RJ1.TD+, RN1.2 (1)
TD-: IC3.16 (TPOUT-), RJ1.TD-, RN1.1
TXLED: IC2.22 (PD5(XCK/CTS)), TX.A
VCC: IC2.14 (VCC), IC2.24 (AVCC), IC2.34 (VCC1), IC2.44 (AVCC1), IC4.P$3 (SEL), IC4.P$4 (PROG2), IC4.P$9 (/TE), IC4.P$17 (CE), L2.2, R1.2
VIN: C17.1, C18.+, CON1.10, CON2.10, CON3.10, D3.C, D5.C, IC2.7 (VBUS), IC4.P$18 (IN1), IC4.P$19 (IN2), JP2.2, JP3.7, R11.2, R12.2, R13.2
VIS-NIR-ADDR: JP6.5, U2.ADR (ADDRSEL)
VIS-NIR-INT: JP6.4, U2.INT

Notes on the sheet:
Power
uSD
32u4
Connectors
ICSP
Ethernet
Breakout
RTC
RGB+Clear
White + NIR
Pressure
Charge Rate = 1000V/PROG1
1.0K = 1000mA
2.0K = 500mA
Humidity
on/off switch
VCC goes through the battery controller, in any case
SENSORS

Board: 2 copper layers, 77 parts (0 on the bottom side), 77 nets, no tracks yet.
