DanBar1971/open-lab-monitor/pcb/eagle/OLM-sensorBoardA.brd

## EAGLE design pcb/eagle/OLM-sensorBoardA.brd (2013-07-11)

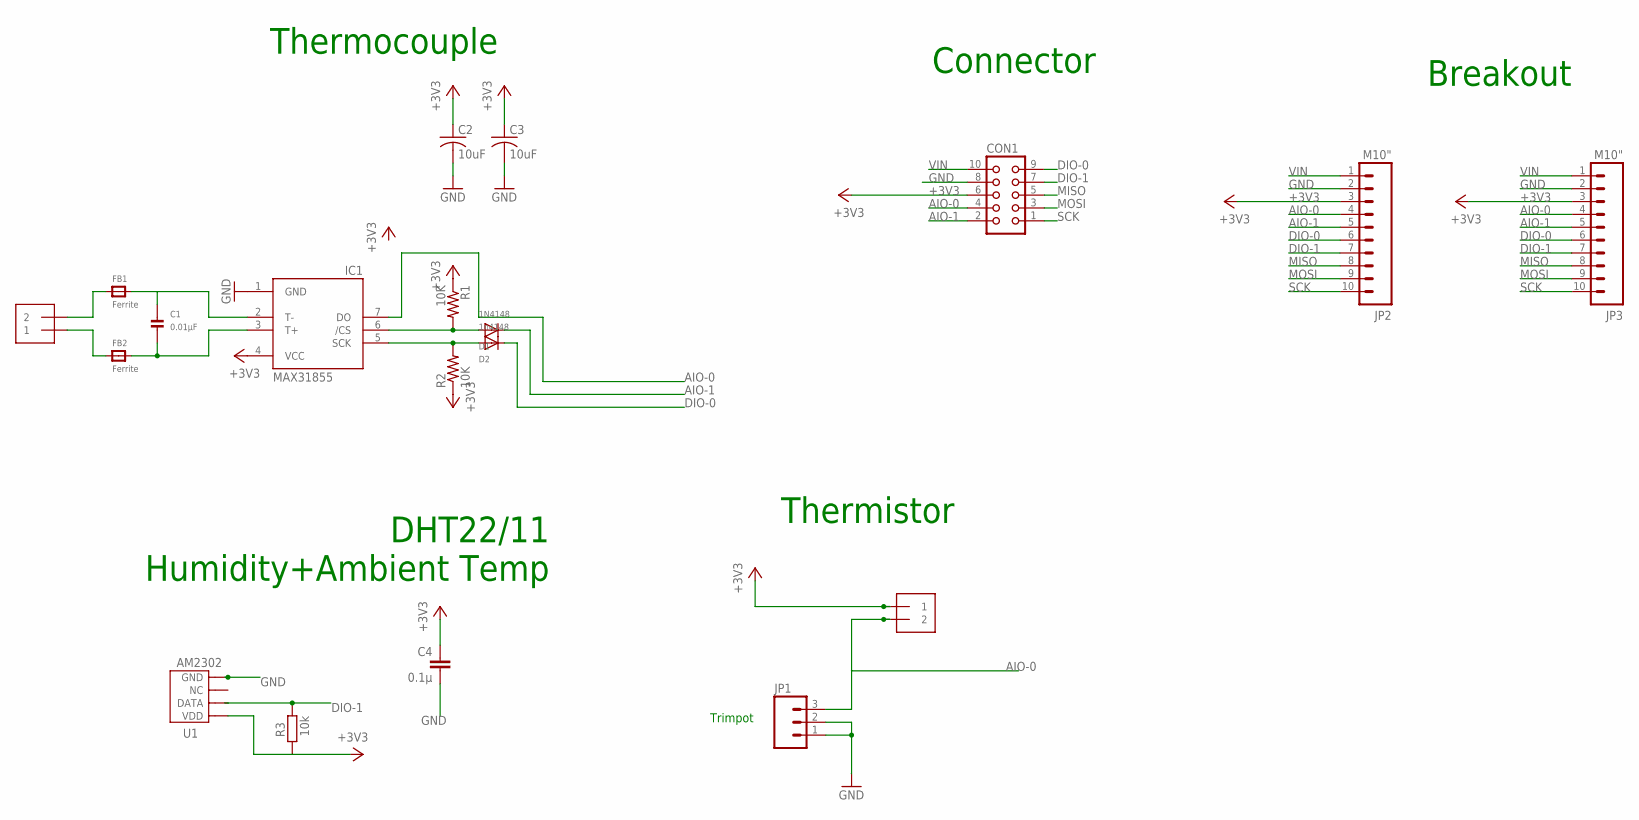
[picture p36: schematic OLM-sensorBoardA.sch]

Parts:
C1: 0.01µF; _0805
C2, C3: 10uF; C0805K
C4: 0.1µ; C025-024X044
CON1: CON10L
D1: 1N4148; SOD-323F
D2: 1n4148; SOD-323F
FB1, FB2: Ferrite; _0805
IC1: MAX31855; SO08
J1, J2: 1X2-3.5MM
JP1: M03PTH; 1X03
JP2, JP3: M10"; 1X10
R1, R2: 10K; R0805
R3: 10k; 0204/7
U1: AM2302

Connections:
+3V3: C2.1, C3.1, C4.1, CON1.6, IC1.4 (VCC), J2.1, JP2.3, JP3.3, R1.1, R2.1, R3.1, U1.P$1 (VDD)
AIO-0: CON1.4, IC1.7 (DO), J2.2, JP1.3, JP2.4, JP3.4
AIO-1: CON1.2, D1.C, JP2.5, JP3.5
CS: D1.A, IC1.6 (/CS), R1.2
DIO-0: CON1.9, D2.C, JP2.6, JP3.6
DIO-1: CON1.7, JP2.7, JP3.7, R3.2, U1.P$2 (DATA)
GND: C2.2, C3.2, C4.2, CON1.8, IC1.1 (GND), JP1.1, JP1.2, JP2.2, JP3.2, U1.P$4 (GND)
MISO: CON1.5, JP2.8, JP3.8
MOSI: CON1.3, JP2.9, JP3.9
unnamed: FB1.1, J1.2
unnamed: C1.1, FB1.2, IC1.2 (T-)
unnamed: FB2.1, J1.1
unnamed: C1.2, FB2.2, IC1.3 (T+)
SCK: CON1.1, D2.A, IC1.5 (SCK), JP2.10, JP3.10, R2.2
VIN: CON1.10, JP2.1, JP3.1

Notes on the sheet:
Thermistor
DHT22/11 Humidity+Ambient Temp
Trimpot
Thermocouple
Connector
Breakout

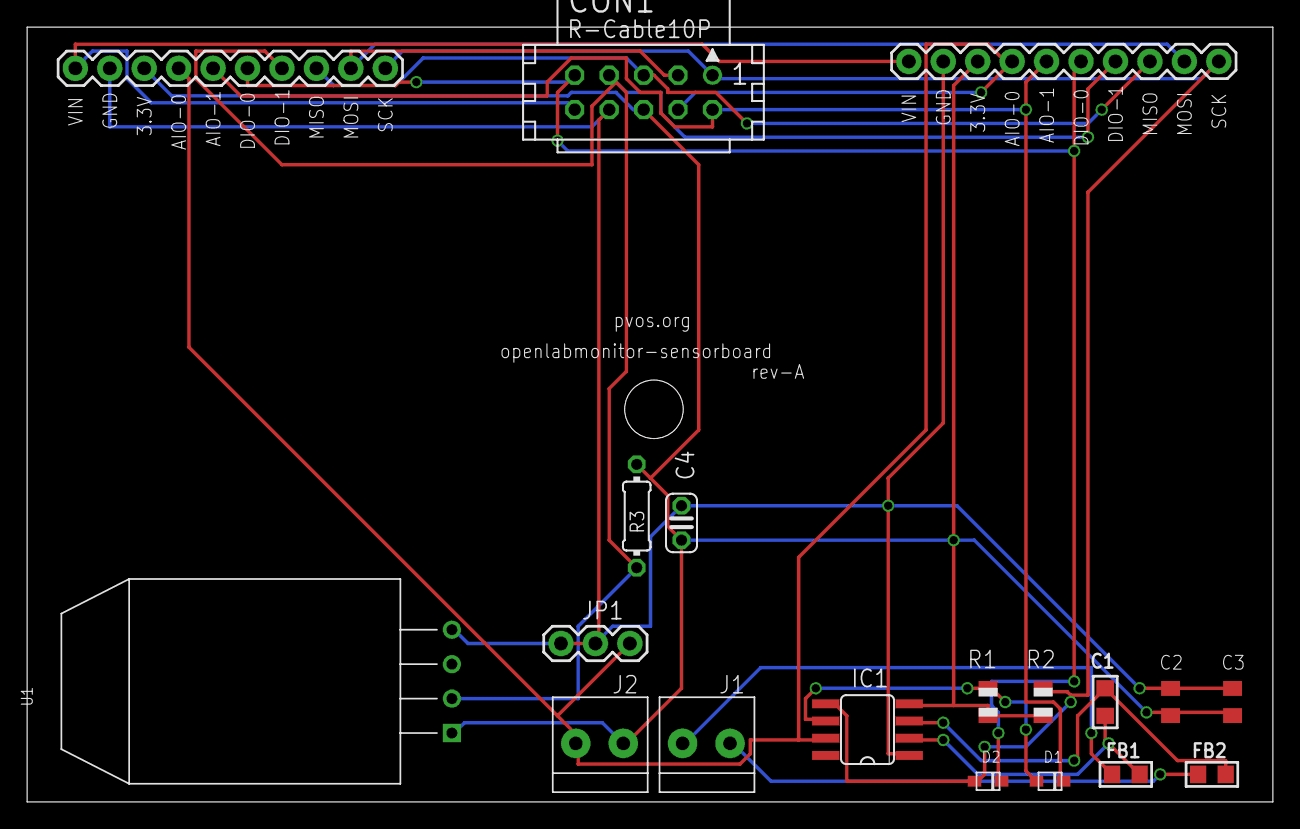
[picture p37: board OLM-sensorBoardA.brd from above]

Board: 2 copper layers, 91.9 x 57.1 mm, 19 parts (0 on the bottom side), 15 nets.
