DanBar1971/open-lab-monitor/pcb/eagle/OLM-env-sensor-REVD.brd

## EAGLE design pcb/eagle/OLM-env-sensor-REVD.brd (2013-07-02)

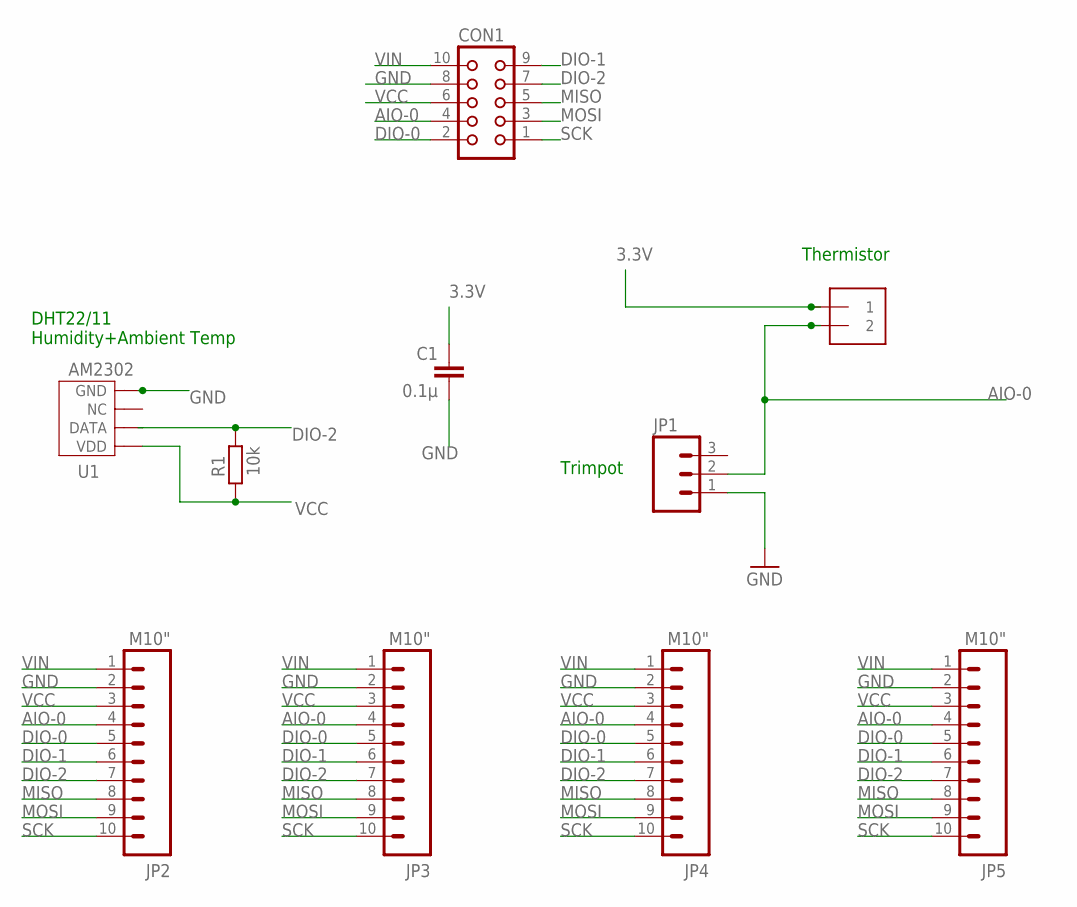
[picture p38: schematic OLM-env-sensor-REVD.sch]

Parts:
C1: 0.1µ; C025-024X044
CON1: CON10L
J1: 1X2-3.5MM
JP1: M03PTH; 1X03
JP2, JP3, JP4, JP5: M10"; 1X10
R1: 10k; 0204/7
U1: AM2302

Connections:
3.3V: C1.1, J1.1
AIO-0: CON1.4, J1.2, JP1.2, JP2.4, JP3.4, JP4.4, JP5.4
DIO-0: CON1.2, JP2.5, JP3.5, JP4.5, JP5.5
DIO-1: CON1.9, JP2.6, JP3.6, JP4.6, JP5.6
DIO-2: CON1.7, JP2.7, JP3.7, JP4.7, JP5.7, R1.2, U1.P$2 (DATA)
GND: C1.2, CON1.8, JP1.1, JP2.2, JP3.2, JP4.2, JP5.2, U1.P$4 (GND)
MISO: CON1.5, JP2.8, JP3.8, JP4.8, JP5.8
MOSI: CON1.3, JP2.9, JP3.9, JP4.9, JP5.9
SCK: CON1.1, JP2.10, JP3.10, JP4.10, JP5.10
VCC: CON1.6, JP2.3, JP3.3, JP4.3, JP5.3, R1.1, U1.P$1 (VDD)
VIN: CON1.10, JP2.1, JP3.1, JP4.1, JP5.1

Notes on the sheet:
Thermistor
DHT22/11 Humidity+Ambient Temp
Trimpot

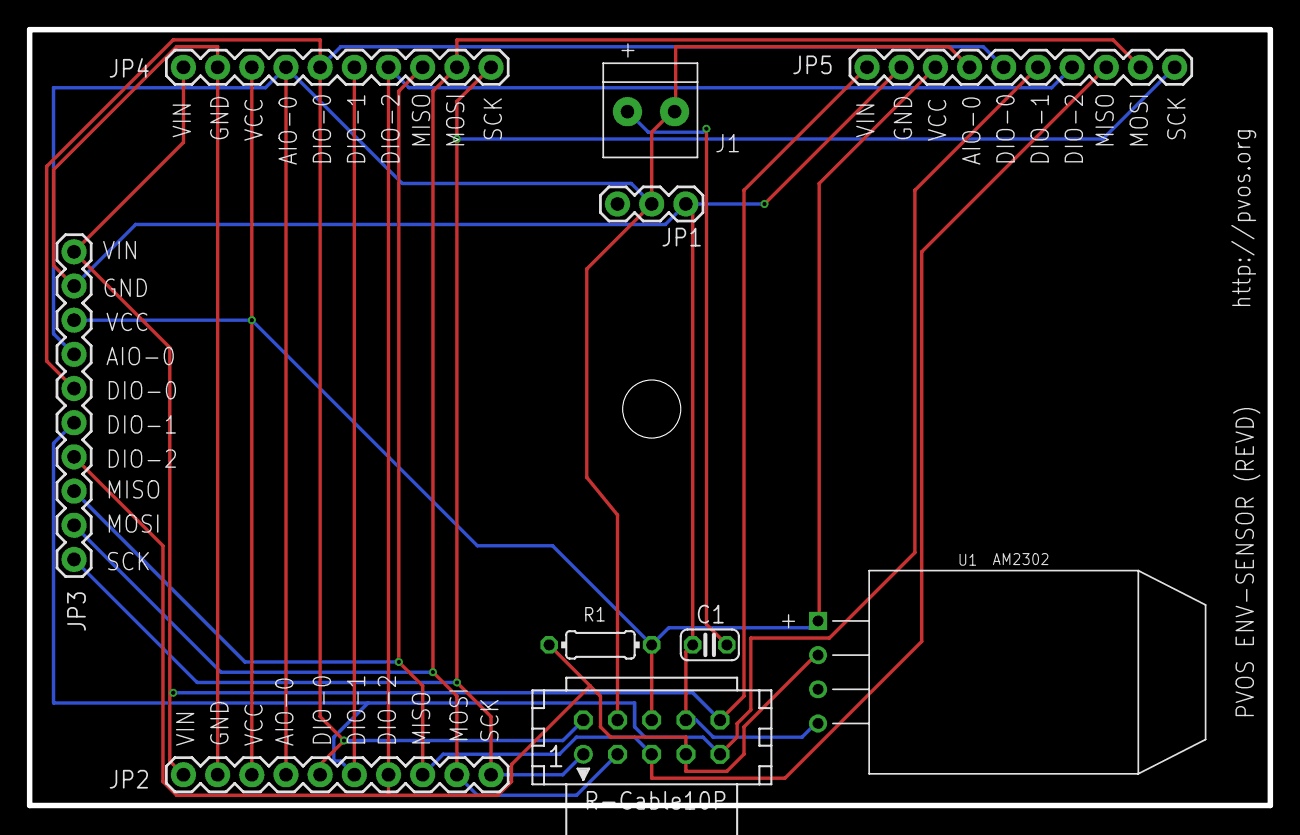
[picture p39: board OLM-env-sensor-REVD.brd from above]

Board: 2 copper layers, 92.2 x 57.7 mm, 10 parts (0 on the bottom side), 11 nets.
