DanBar1971/open-lab-monitor/pcb/reference/wings20.brd

## EAGLE design pcb/reference/wings20.brd (2013-06-24)

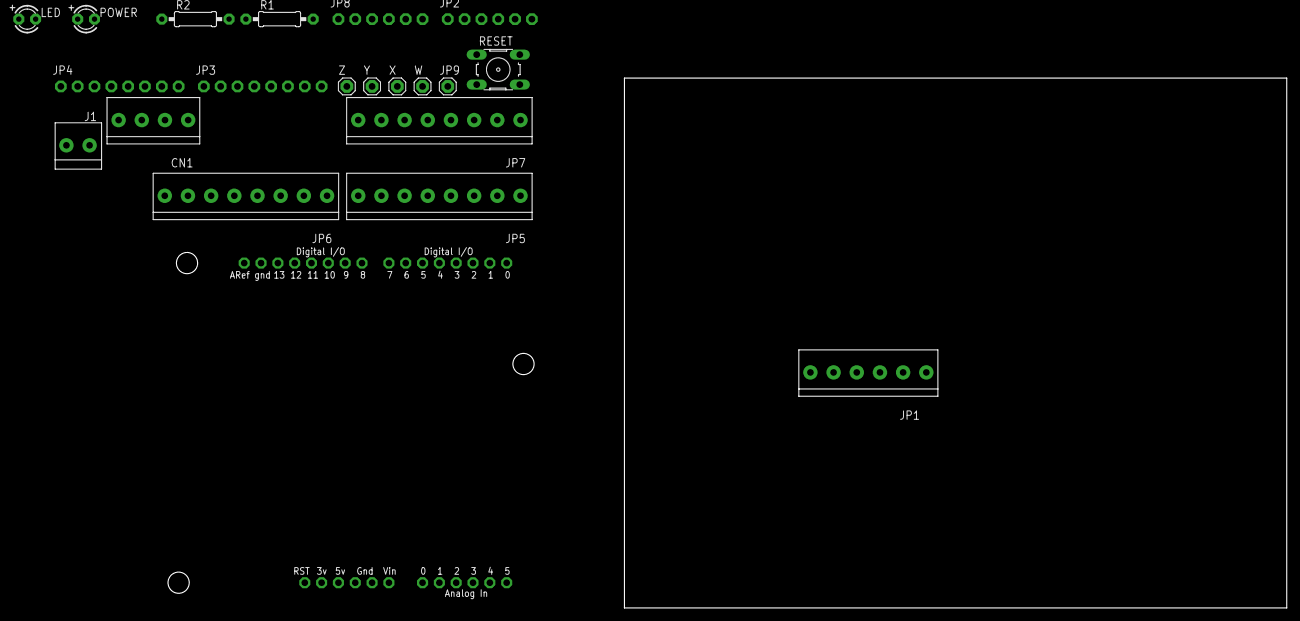
[picture p40: board wings20.brd from above]

Board: 2 copper layers, 100.0 x 80.0 mm, 21 parts (0 on the bottom side), 33 nets, no tracks yet.

Parts:
CN1: 1X4-3.5MM; 1X04-3.5MM
J1: 1X2-3.5MM
JP1: 1X06-3.5MM
JP2, JP8: 1X06-CLEANBIG
JP3, JP4: 1X08-CLEANBIG
JP5, JP6, JP7: 1X08-3.5MM
JP9: 1X01
LED: LED3MM
POWER: LED3MM
R1, R2: 0207/10
RESET: B3F-10XX
U$1: ARDUINO-BPLACE
W: 1X01
X: 1X01
Y: 1X01
Z: 1X01

Connections:
3V: JP1.2, JP8.5, U$1.3V
GND: J1.1, J1.2, JP1.4, JP1.5, JP4.2, JP6.7, JP7.7, JP7.8, JP8.2, JP8.3, R1.1, R2.1, RESET.3, RESET.4, U$1.GND, U$1.GND1, U$1.GND2
unnamed: JP3.1, JP5.8, U$1.D7
unnamed: JP3.2, JP5.7, U$1.D6
unnamed: JP3.3, JP5.6, U$1.D5
unnamed: JP3.4, JP5.5, U$1.D4
unnamed: JP3.5, JP5.4, U$1.D3
unnamed: JP3.6, JP5.3, U$1.D2
unnamed: JP3.7, JP5.2, U$1.D1
unnamed: JP3.8, JP5.1, U$1.D0
unnamed: JP4.1, JP6.8, U$1.AREF
unnamed: LED.K, R1.2
unnamed: JP4.3, JP6.6, U$1.D13
unnamed: JP4.4, JP6.5, U$1.D12
unnamed: JP4.5, JP6.4, U$1.D11
unnamed: JP4.6, JP6.3, U$1.D10
unnamed: JP4.7, JP6.2, U$1.D9
unnamed: JP4.8, JP6.1, U$1.D8
unnamed: JP2.1, JP7.6, U$1.A5
unnamed: JP2.2, JP7.5, U$1.A4
unnamed: JP2.3, JP7.4, U$1.A3
unnamed: JP2.4, JP7.3, U$1.A2
unnamed: JP2.5, JP7.2, U$1.A1
unnamed: JP2.6, JP7.1, U$1.A0
unnamed: POWER.K, R2.2
unnamed: JP9.1, LED.A
unnamed: CN1.4, Z.1
unnamed: JP1.1, JP8.6, RESET.1, RESET.2, U$1.RESET
unnamed: CN1.3, Y.1
unnamed: CN1.2, X.1
unnamed: CN1.1, W.1
VCC: JP1.3, JP8.4, POWER.A, U$1.5V
VIN: JP1.6, JP8.1, U$1.VIN
