DanBar1971/open-lab-monitor/pcb/reference/SprinklerControllerRecover.brd

## EAGLE design pcb/reference/SprinklerControllerRecover.brd (2013-06-24)

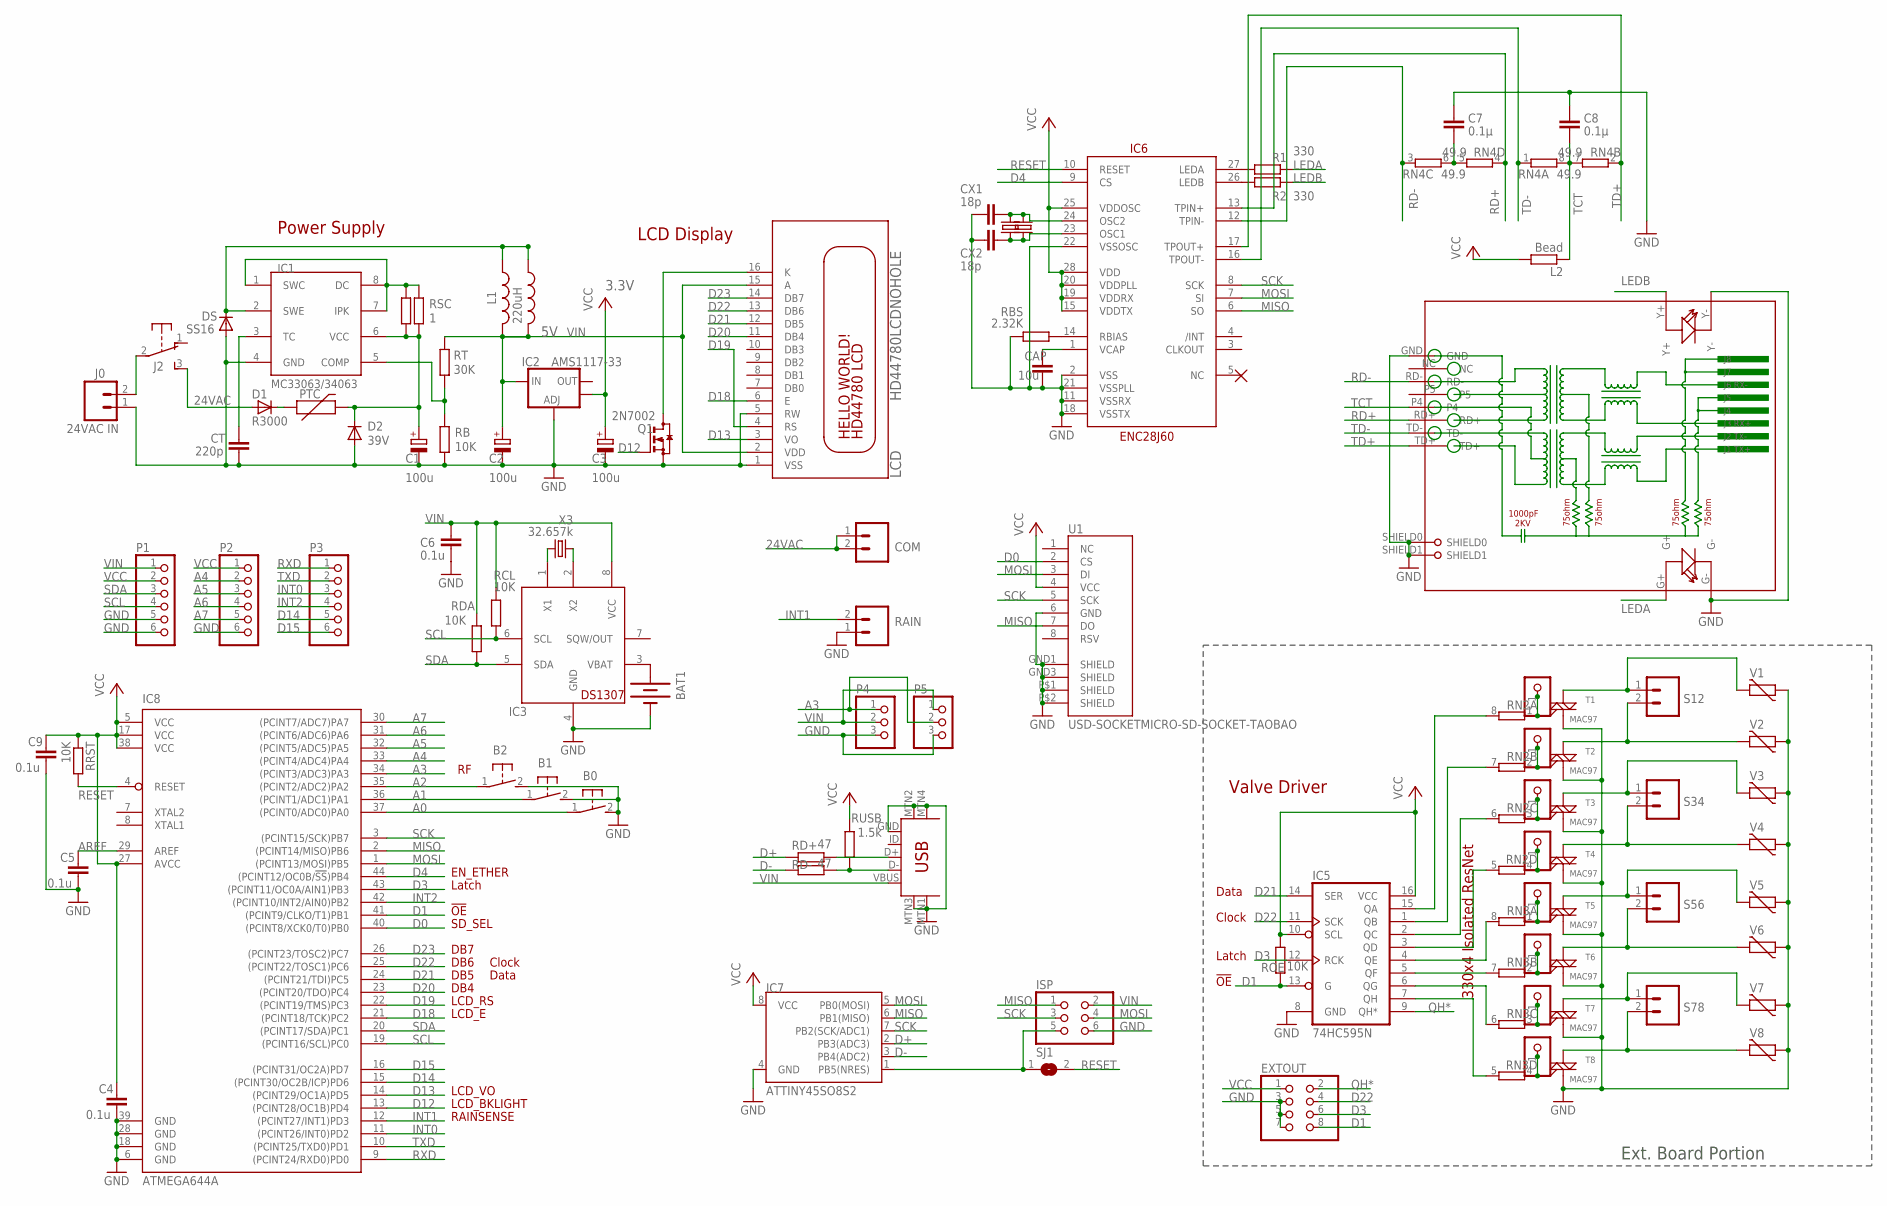
[picture p41: schematic SprinklerControllerRecover.sch]

Parts:
B0, B1, B2: 31-XX; B3F-31XX
BAT1: BATTERYBATTERY_12MM_SMT; BATTCON_12MM_SMT
C1: 100u; E3,5-8
C2, C3: 100u; E2,5-5
C4, C5, C6, C9: 0.1u; C0805
C7, C8: 0.1µ; C0805
CAP: 10u; C0805
COM: M025MM; SCREWTERMINAL-5MM-2
CT: 220p; C0805
CX1, CX2: 18p; C0805
D1: R3000; DO41-7.6
D2: 39V; DO41-7.6
DS: SS16; DO214AC
EXTOUT: PINHD-2X4; 2X04
IC1: MC34063; SO08
IC2: AMS1117-33; SOT223
IC3: DS1307; SO08
IC5: 74HC595N; SO16
IC6: ENC28J60; SOIC28WLONG
IC7: ATTINY45SO8S2; SO8S2
IC8: ATMEGA644A; TQFP44
ISP: PINHD-2X3; 2X03
J0: 24VAC IN; SCREWTERMINAL-5MM-2
J2: EG1206
JP2, JP3, JP4, JP5, JP6, JP7, JP8, JP9: PINHD-1X1CB; 1X01-CLEANBIG
L1: 220uH; 6000-XXXX-RC
L2: Bead; R0805
L3: 220uH; SRU1038
LCD: HD44780LCDNOHOLE; LCD1602A
P1, P2, P3: PINHD-1X6CLEAN; 1X06-CLEAN
P4, P5: PINHD-1X3; 1X03
PTC: PTC
Q1: 2N7002; SOT23
R1, R2: 330; R0805
RAIN: M025MM; SCREWTERMINAL-5MM-2
RB: 10K; R0805
RBS: 2.32K; R0805
RCL: 10K; R0805
RD+: 47; R0805
RD-: 47; R0805
RDA: 10K; R0805
RJ1: HR911105A
RN2, RN3: 4R-NEXB38V; EXB38V
RN4: 49.9; EXB38V
ROE: 10K; R0805
RRST: 10K; R0805
RSC: 1; R0805
RSC1: 1.0; R0805
RT: 30K; R0805
RUSB: 1.5k; R0805
S12, S34, S56, S78: M025MM; SCREWTERMINAL-5MM-2
SJ1: SJ
T1, T2, T3, T4, T5, T6, T7, T8: MAC97; SOT223
U1: USD-SOCKETMICRO-SD-SOCKET-TAOBAO; MICRO-SD-SOCKET-TAOBAO
U$1: USB-MINIB-5PIN; USB-MINIB
V1, V2, V3, V4, V5, V6, V7, V8: MOV; R-5
X2A: 25MHz; CRYSTAL-SMD-10.5X4.8-2PIN
X2A1: 25MHz; HC49US
X3: 32.657k; TC26H

Connections:
24VAC: COM.1, COM.2, D1.A, J2.3 (S)
A0: B0.1, IC8.37 ((PCINT0/ADC0)PA0)
A1: B1.1, IC8.36 ((PCINT1/ADC1)PA1)
A2: B2.1, IC8.35 ((PCINT2/ADC2)PA2)
A3: IC8.34 ((PCINT3/ADC3)PA3), P4.1, P5.2
A4: IC8.33 ((PCINT4/ADC4)PA4), P2.2
A5: IC8.32 ((PCINT5/ADC5)PA5), P2.3
A6: IC8.31 ((PCINT6/ADC6)PA6), P2.4
A7: IC8.30 ((PCINT7/ADC7)PA7), P2.5
AREF: C5.1, IC8.29 (AREF)
D0: IC8.40 ((PCINT8/XCK0/T0)PB0), U1.2 (CS)
D1: EXTOUT.8, IC5.13 (G), IC8.41 ((PCINT9/CLKO/T1)PB1), ROE.1
D3: EXTOUT.6, IC5.12 (RCK), IC8.43 ((PCINT11/OC0A/AIN1)PB3)
D4: IC6.9 (CS), IC8.44 ((PCINT12/OC0B/!SS!)PB4)
D12: IC8.13 ((PCINT28/OC1B)PD4), Q1.1 (G)
D13: IC8.14 ((PCINT29/OC1A)PD5), LCD.3 (VO)
D14: IC8.15 ((PCINT30/OC2B/ICP)PD6), P3.5
D15: IC8.16 ((PCINT31/OC2A)PD7), P3.6
D18: IC8.21 ((PCINT18/TCK)PC2), LCD.6 (E)
D19: IC8.22 ((PCINT19/TMS)PC3), LCD.4 (RS)
D20: IC8.23 ((PCINT20/TDO)PC4), LCD.11 (DB4)
D21: IC5.14 (SER), IC8.24 ((PCINT21/TDI)PC5), LCD.12 (DB5)
D22: EXTOUT.4, IC5.11 (SCK), IC8.25 ((PCINT22/TOSC1)PC6), LCD.13 (DB6)
D23: IC8.26 ((PCINT23/TOSC2)PC7), LCD.14 (DB7)
D+: IC7.2 (PB3(ADC3)), RD+.1
D-: IC7.3 (PB4(ADC2)), RD-.1
GND: B0.2 (S), B1.2 (S), B2.2 (S), BAT1.P$1 (-), C1.-, C2.-, C3.-, C4.2, C5.2, C6.2, C7.1, C8.1, C9.2, CAP.2, CT.2, CX1.2, CX2.2, D2.A, DS.A, EXTOUT.3, EXTOUT.5, EXTOUT.7, IC1.4 (GND), IC2.1 (ADJ), IC3.4 (GND), IC5.8 (GND), IC6.2 (VSS), IC6.11 (VSSRX), IC6.18 (VSSTX), IC6.21 (VSSPLL), IC6.22 (VSSOSC), IC7.4 (GND), IC8.6 (GND), IC8.18 (GND), IC8.28 (GND), IC8.39 (GND), ISP.6, J0.1, LCD.1 (VSS), LCD.5 (RW), P1.5, P1.6, P2.6, P4.3, P5.3, Q1.2 (S), RAIN.1, RB.2, RBS.1, RJ1.G-, RJ1.GND, RJ1.SHIELD0, RJ1.SHIELD1, RJ1.Y-, T1.1 (M1), T2.1 (M1), T3.1 (M1), T4.1 (M1), T5.1 (M1), T6.1 (M1), T7.1 (M1), T8.1 (M1), U1.6 (GND), U1.GND1 (SHIELD), U1.GND3 (SHIELD), U1.P$1 (SHIELD), U1.P$2 (SHIELD), U$1.GND, U$1.MTN1 (MTN2), U$1.MTN2 (MTN3), U$1.MTN3 (MTN1), U$1.MTN4, V1.1, V2.1, V3.1, V4.1, V5.1, V6.1, V7.1, V8.1
INT0: IC8.11 ((PCINT26/INT0)PD2), P3.3
INT1: IC8.12 ((PCINT27/INT1)PD3), RAIN.2
INT2: IC8.42 ((PCINT10/INT2/AIN0)PB2), P3.4
LEDA: R1.2, RJ1.G+
LEDB: R2.2, RJ1.Y+
MISO: IC6.6 (SO), IC7.6 (PB1(MISO)), IC8.2 ((PCINT14/MISO)PB6), ISP.1, U1.7 (DO)
MOSI: IC6.7 (SI), IC7.5 (PB0(MOSI)), IC8.1 ((PCINT13/MOSI)PB5), ISP.4, U1.3 (DI)
unnamed: D1.C, PTC.P$1 (1)
unnamed: JP2.1, RN2.1, T1.3 (G)
unnamed: IC5.5 (QF), RN3.7 (2)
unnamed: IC5.6 (QG), RN3.6 (2)
unnamed: J0.2, J2.2
unnamed: IC5.7 (QH), RN3.5 (2)
unnamed: C1.+, D2.C, IC1.6 (VCC), PTC.P$2 (2), RSC.2, RSC1.2
unnamed: IC5.4 (QE), RN3.8 (2)
unnamed: IC5.3 (QD), RN2.5 (2)
unnamed: IC5.2 (QC), RN2.6 (2)
unnamed: IC5.1 (QB), RN2.7 (2)
unnamed: IC5.15 (QA), RN2.8 (2)
unnamed: JP3.1, RN2.2 (1), T2.3 (G)
unnamed: S12.1, T1.4 (M2), V1.2
unnamed: S12.2, T2.4 (M2), V2.2
unnamed: S34.1, T3.4 (M2), V3.2
unnamed: JP4.1, RN2.3 (1), T3.3 (G)
unnamed: S34.2, T4.4 (M2), V4.2
unnamed: JP5.1, RN2.4 (1), T4.3 (G)
unnamed: S56.1, T5.4 (M2), V5.2
unnamed: S56.2, T6.4 (M2), V6.2
unnamed: S78.1, T7.4 (M2), V7.2
unnamed: S78.2, T8.4 (M2), V8.2
unnamed: JP6.1, RN3.1, T5.3 (G)
unnamed: JP7.1, RN3.2 (1), T6.3 (G)
unnamed: JP8.1, RN3.3 (1), T7.3 (G)
unnamed: JP9.1, RN3.4 (1), T8.3 (G)
unnamed: IC6.27 (LEDA), R1.1
unnamed: BAT1.P$2 (+), IC3.3 (VBAT)
unnamed: IC6.26 (LEDB), R2.1
unnamed: RD+.2, U$1.D+
unnamed: CAP.1, IC6.1 (VCAP)
unnamed: IC1.1 (SWC), IC1.7 (IPK), IC1.8 (DC), RSC.1, RSC1.1
unnamed: CX1.1, IC6.24 (OSC2), X2A.P$2 (2), X2A1.2
unnamed: CX2.1, IC6.23 (OSC1), X2A.P$1 (1), X2A1.1
unnamed: RD-.2, RUSB.1, U$1.D-
unnamed: DS.C, IC1.2 (SWE), L1.1, L3.1
unnamed: IC3.1 (X1), X3.1
unnamed: CT.1, IC1.3 (TC)
unnamed: IC3.2 (X2), X3.2
unnamed: IC7.1 (PB5(NRES)), ISP.5, SJ1.1
unnamed: C7.2, RN4.5 (2), RN4.6 (2)
unnamed: IC1.5 (COMP), RB.1, RT.2
unnamed: LCD.16 (K), Q1.3 (D)
unnamed: IC6.14 (RBIAS), RBS.2
QH*: EXTOUT.2, IC5.9 (QH*)
RD+: IC6.13 (TPIN+), RJ1.RD+, RN4.4 (1)
RD-: IC6.12 (TPIN-), RJ1.RD-, RN4.3 (1)
RESET: IC6.10 (RESET), IC8.4 (RESET), RRST.2, SJ1.2
RXD: IC8.9 ((PCINT24/RXD0)PD0), P3.1
SCK: IC6.8 (SCK), IC7.7 (PB2(SCK/ADC1)), IC8.3 ((PCINT15/SCK)PB7), ISP.3, U1.5 (SCK)
SCL: IC3.6 (SCL), IC8.19 ((PCINT16/SCL)PC0), P1.4, RCL.2
SDA: IC3.5 (SDA), IC8.20 ((PCINT17/SDA)PC1), P1.3, RDA.2
TCT: C8.2, L2.1, RJ1.P4, RN4.7 (2), RN4.8 (2)
TD+: IC6.17 (TPOUT+), RJ1.TD+, RN4.2 (1)
TD-: IC6.16 (TPOUT-), RJ1.TD-, RN4.1
TXD: IC8.10 ((PCINT25/TXD0)PD1), P3.2
VCC: C3.+, C4.1, C9.1, EXTOUT.1, IC2.4 (OUT), IC5.10 (SCL), IC5.16 (VCC), IC6.15 (VDDTX), IC6.19 (VDDRX), IC6.20 (VDDPLL), IC6.25 (VDDOSC), IC6.28 (VDD), IC7.8 (VCC), IC8.5 (VCC), IC8.17 (VCC), IC8.27 (AVCC), IC8.38 (VCC), L2.2, P1.2, P2.1, ROE.2, RRST.1, RUSB.2, U1.4 (VCC)
VIN: C2.+, C6.1, IC2.3 (IN), IC3.8 (VCC), ISP.2, L1.2, L3.2, LCD.2 (VDD), LCD.15 (A), P1.1, P4.2, P5.1, RCL.1, RDA.1, RT.1, U$1.VBUS

Notes on the sheet:
Power Supply
Valve Driver
Data
Clock
Latch
DB4
330x4 Isolated ResNet
LCD Display
EN_ETHER
3.3V
DB7
LCD_E
LCD_RS
DB6
DB5
Ext. Board Portion
!OE
RAINSENSE
LCD_BKLIGHT
LCD_VO
SD_SEL

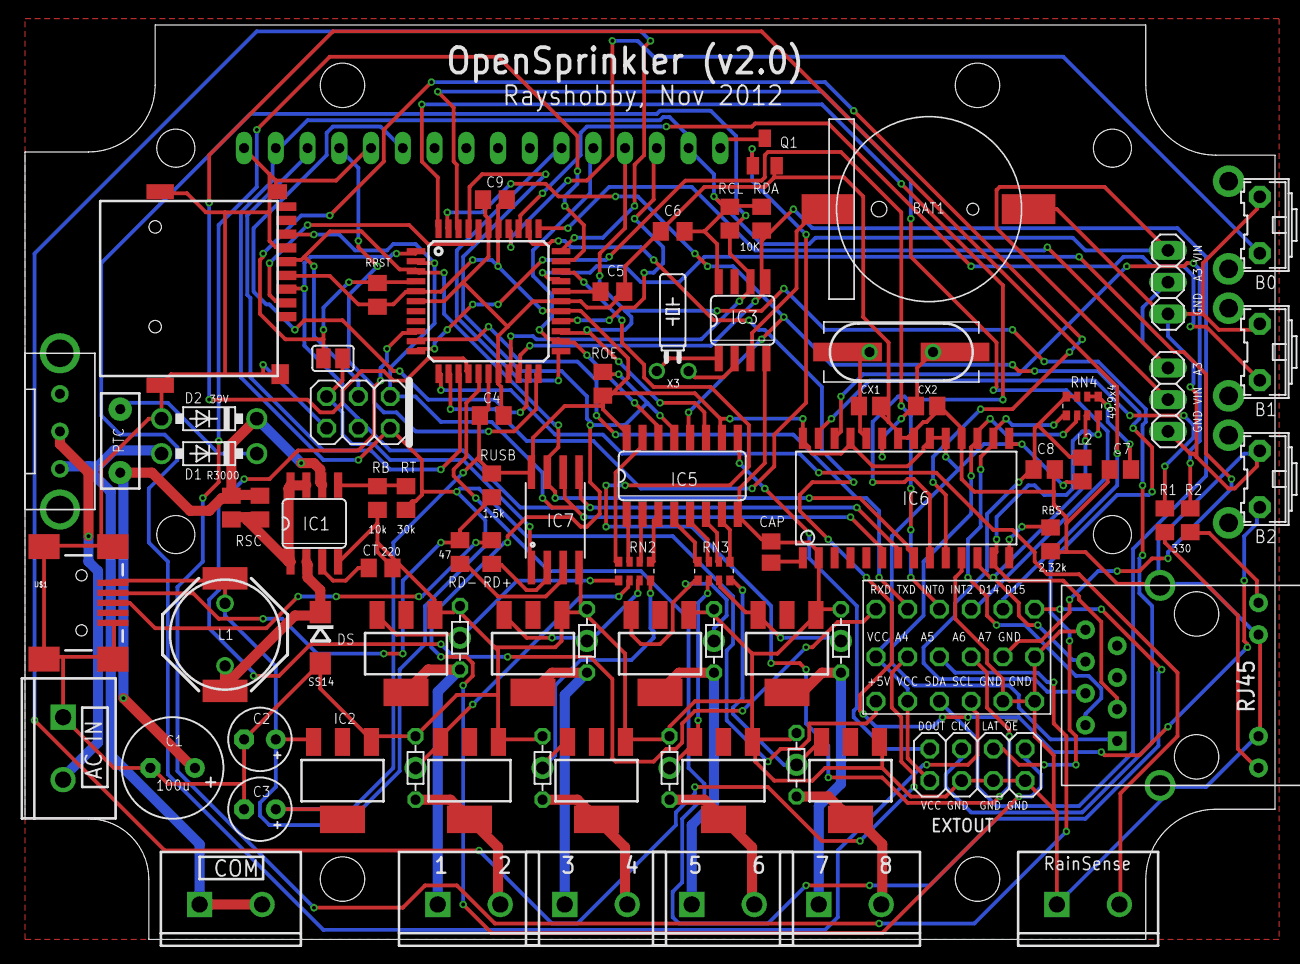
[picture p42: board SprinklerControllerRecover.brd from above]

Board: 2 copper layers, 100.0 x 73.2 mm, 96 parts (0 on the bottom side), 93 nets.
